peng-zhihui/L-ink_Card/DAP-Link/Firmware/src/source/cmsis-core/core_armv81mml.h

/**************************************************************************//**
 * @file     core_armv81mml.h
 * @brief    CMSIS Armv8.1-M Mainline Core Peripheral Access Layer Header File
 * @version  V1.2.0
 * @date     21. October 2019
 ******************************************************************************/
/*
 * Copyright (c) 2018-2019 Arm Limited. All rights reserved.
 *
 * SPDX-License-Identifier: Apache-2.0
 *
 * Licensed under the Apache License, Version 2.0 (the License); you may
 * not use this file except in compliance with the License.
 * You may obtain a copy of the License at
 *
 * www.apache.org/licenses/LICENSE-2.0
 *
 * Unless required by applicable law or agreed to in writing, software
 * distributed under the License is distributed on an AS IS BASIS, WITHOUT
 * WARRANTIES OR CONDITIONS OF ANY KIND, either express or implied.
 * See the License for the specific language governing permissions and
 * limitations under the License.
 */

#if   defined ( __ICCARM__ )
  #pragma system_include         /* treat file as system include file for MISRA check */
#elif defined (__clang__)
  #pragma clang system_header   /* treat file as system include file */
#endif

#ifndef __CORE_ARMV81MML_H_GENERIC
#define __CORE_ARMV81MML_H_GENERIC

#include <stdint.h>

#ifdef __cplusplus
 extern "C" {
#endif

/**
  \page CMSIS_MISRA_Exceptions  MISRA-C:2004 Compliance Exceptions
  CMSIS violates the following MISRA-C:2004 rules:

   \li Required Rule 8.5, object/function definition in header file.<br>
     Function definitions in header files are used to allow 'inlining'.

   \li Required Rule 18.4, declaration of union type or object of union type: '{...}'.<br>
     Unions are used for effective representation of core registers.

   \li Advisory Rule 19.7, Function-like macro defined.<br>
     Function-like macros are used to allow more efficient code.
 */


/*******************************************************************************
 *                 CMSIS definitions
 ******************************************************************************/
/**
  \ingroup Cortex_ARMV81MML
  @{
 */

#include "cmsis_version.h"
 
#define __ARM_ARCH_8M_MAIN__    1  // patching for now
/*  CMSIS ARMV81MML definitions */
#define __ARMv81MML_CMSIS_VERSION_MAIN  (__CM_CMSIS_VERSION_MAIN)                   /*!< \deprecated [31:16] CMSIS HAL main version */
#define __ARMv81MML_CMSIS_VERSION_SUB   (__CM_CMSIS_VERSION_SUB)                    /*!< \deprecated [15:0]  CMSIS HAL sub version */
#define __ARMv81MML_CMSIS_VERSION       ((__ARMv81MML_CMSIS_VERSION_MAIN << 16U) | \
                                         __ARMv81MML_CMSIS_VERSION_SUB           )  /*!< \deprecated CMSIS HAL version number */

#define __CORTEX_M                     (81U)                                       /*!< Cortex-M Core */

#if defined ( __CC_ARM )
  #error Legacy Arm Compiler does not support Armv8.1-M target architecture.
#elif defined (__ARMCC_VERSION) && (__ARMCC_VERSION >= 6010050)
  #if defined __ARM_FP
    #if defined (__FPU_PRESENT) && (__FPU_PRESENT == 1U)
      #define __FPU_USED       1U
    #else
      #error "Compiler generates FPU instructions for a device without an FPU (check __FPU_PRESENT)"
      #define __FPU_USED       0U
    #endif
  #else
    #define __FPU_USED         0U
  #endif

  #if defined(__ARM_FEATURE_DSP)
    #if defined(__DSP_PRESENT) && (__DSP_PRESENT == 1U)
      #define __DSP_USED       1U
    #else
      #error "Compiler generates DSP (SIMD) instructions for a devices without DSP extensions (check __DSP_PRESENT)"
      #define __DSP_USED         0U    
    #endif
  #else
    #define __DSP_USED         0U
  #endif
  
  #if defined(__ARM_FEATURE_MVE)
    #if defined(__MVE_PRESENT) && (__MVE_PRESENT == 1U)
      #define __MVE_USED       1U
    #else
      #error "Compiler generates MVE instructions for a devices without MVE extensions (check __MVE_PRESENT)"
      #define __MVE_USED         0U    
    #endif
  #else
    #define __MVE_USED         0U
  #endif

#elif defined ( __GNUC__ )
  #if defined (__VFP_FP__) && !defined(__SOFTFP__)
    #if defined (__FPU_PRESENT) && (__FPU_PRESENT == 1U)
      #define __FPU_USED       1U
    #else
      #error "Compiler generates FPU instructions for a device without an FPU (check __FPU_PRESENT)"
      #define __FPU_USED       0U
    #endif
  #else
    #define __FPU_USED         0U
  #endif
  
  #if defined(__ARM_FEATURE_DSP)
    #if defined(__DSP_PRESENT) && (__DSP_PRESENT == 1U)
      #define __DSP_USED       1U
    #else
      #error "Compiler generates DSP (SIMD) instructions for a devices without DSP extensions (check __DSP_PRESENT)"
      #define __DSP_USED         0U    
    #endif
  #else
    #define __DSP_USED         0U
  #endif
    
  #if defined(__ARM_FEATURE_MVE)
    #if defined(__MVE_PRESENT) && (__MVE_PRESENT == 1U)
      #define __MVE_USED       1U
    #else
      #error "Compiler generates MVE instructions for a devices without MVE extensions (check __MVE_PRESENT)"
      #define __MVE_USED         0U    
    #endif
  #else
    #define __MVE_USED         0U
  #endif
  
#elif defined ( __ICCARM__ )
  #if defined __ARMVFP__
    #if defined (__FPU_PRESENT) && (__FPU_PRESENT == 1U)
      #define __FPU_USED       1U
    #else
      #error "Compiler generates FPU instructions for a device without an FPU (check __FPU_PRESENT)"
      #define __FPU_USED       0U
    #endif
  #else
    #define __FPU_USED         0U
  #endif

  #if defined(__ARM_FEATURE_DSP)
    #if defined(__DSP_PRESENT) && (__DSP_PRESENT == 1U)
      #define __DSP_USED       1U
    #else
      #error "Compiler generates DSP (SIMD) instructions for a devices without DSP extensions (check __DSP_PRESENT)"
      #define __DSP_USED         0U    
    #endif
  #else
    #define __DSP_USED         0U
  #endif

  #if defined(__ARM_FEATURE_MVE)
    #if defined(__MVE_PRESENT) && (__MVE_PRESENT == 1U)
      #define __MVE_USED       1U
    #else
      #error "Compiler generates MVE instructions for a devices without MVE extensions (check __MVE_PRESENT)"
      #define __MVE_USED         0U    
    #endif
  #else
    #define __MVE_USED         0U
  #endif
  
#elif defined ( __TI_ARM__ )
  #if defined __TI_VFP_SUPPORT__
    #if defined (__FPU_PRESENT) && (__FPU_PRESENT == 1U)
      #define __FPU_USED       1U
    #else
      #error "Compiler generates FPU instructions for a device without an FPU (check __FPU_PRESENT)"
      #define __FPU_USED       0U
    #endif
  #else
    #define __FPU_USED         0U
  #endif

#elif defined ( __TASKING__ )
  #if defined __FPU_VFP__
    #if defined (__FPU_PRESENT) && (__FPU_PRESENT == 1U)
      #define __FPU_USED       1U
    #else
      #error "Compiler generates FPU instructions for a device without an FPU (check __FPU_PRESENT)"
      #define __FPU_USED       0U
    #endif
  #else
    #define __FPU_USED         0U
  #endif

#elif defined ( __CSMC__ )
  #if ( __CSMC__ & 0x400U)
    #if defined (__FPU_PRESENT) && (__FPU_PRESENT == 1U)
      #define __FPU_USED       1U
    #else
      #error "Compiler generates FPU instructions for a device without an FPU (check __FPU_PRESENT)"
      #define __FPU_USED       0U
    #endif
  #else
    #define __FPU_USED         0U
  #endif

#endif

#include "cmsis_compiler.h"               /* CMSIS compiler specific defines */


#ifdef __cplusplus
}
#endif

#endif /* __CORE_ARMV81MML_H_GENERIC */

#ifndef __CMSIS_GENERIC

#ifndef __CORE_ARMV81MML_H_DEPENDANT
#define __CORE_ARMV81MML_H_DEPENDANT

#ifdef __cplusplus
 extern "C" {
#endif

/* check device defines and use defaults */
#if defined __CHECK_DEVICE_DEFINES
  #ifndef __ARMv81MML_REV
    #define __ARMv81MML_REV               0x0000U
    #warning "__ARMv81MML_REV not defined in device header file; using default!"
  #endif

  #ifndef __FPU_PRESENT
    #define __FPU_PRESENT             0U
    #warning "__FPU_PRESENT not defined in device header file; using default!"
  #endif

  #ifndef __MPU_PRESENT
    #define __MPU_PRESENT             0U
    #warning "__MPU_PRESENT not defined in device header file; using default!"
  #endif

  #ifndef __SAUREGION_PRESENT
    #define __SAUREGION_PRESENT       0U
    #warning "__SAUREGION_PRESENT not defined in device header file; using default!"
  #endif

  #ifndef __DSP_PRESENT
    #define __DSP_PRESENT             0U
    #warning "__DSP_PRESENT not defined in device header file; using default!"
  #endif

  #ifndef __MVE_PRESENT
    #define __MVE_PRESENT             0U
    #warning "__MVE_PRESENT not defined in device header file; using default!"
  #endif

  #ifndef __NVIC_PRIO_BITS
    #define __NVIC_PRIO_BITS          3U
    #warning "__NVIC_PRIO_BITS not defined in device header file; using default!"
  #endif

  #ifndef __Vendor_SysTickConfig
    #define __Vendor_SysTickConfig    0U
    #warning "__Vendor_SysTickConfig not defined in device header file; using default!"
  #endif
#endif

/* IO definitions (access restrictions to peripheral registers) */
/**
    \defgroup CMSIS_glob_defs CMSIS Global Defines

    <strong>IO Type Qualifiers</strong> are used
    \li to specify the access to peripheral variables.
    \li for automatic generation of peripheral register debug information.
*/
#ifdef __cplusplus
  #define   __I     volatile             /*!< Defines 'read only' permissions */
#else
  #define   __I     volatile const       /*!< Defines 'read only' permissions */
#endif
#define     __O     volatile             /*!< Defines 'write only' permissions */
#define     __IO    volatile             /*!< Defines 'read / write' permissions */

/* following defines should be used for structure members */
#define     __IM     volatile const      /*! Defines 'read only' structure member permissions */
#define     __OM     volatile            /*! Defines 'write only' structure member permissions */
#define     __IOM    volatile            /*! Defines 'read / write' structure member permissions */

/*@} end of group ARMv81MML */



/*******************************************************************************
 *                 Register Abstraction
  Core Register contain:
  - Core Register
  - Core NVIC Register
  - Core SCB Register
  - Core SysTick Register
  - Core Debug Register
  - Core MPU Register
  - Core SAU Register
  - Core FPU Register
 ******************************************************************************/
/**
  \defgroup CMSIS_core_register Defines and Type Definitions
  \brief Type definitions and defines for Cortex-M processor based devices.
*/

/**
  \ingroup    CMSIS_core_register
  \defgroup   CMSIS_CORE  Status and Control Registers
  \brief      Core Register type definitions.
  @{
 */

/**
  \brief  Union type to access the Application Program Status Register (APSR).
 */
typedef union
{
  struct
  {
    uint32_t _reserved0:16;              /*!< bit:  0..15  Reserved */
    uint32_t GE:4;                       /*!< bit: 16..19  Greater than or Equal flags */
    uint32_t _reserved1:7;               /*!< bit: 20..26  Reserved */
    uint32_t Q:1;                        /*!< bit:     27  Saturation condition flag */
    uint32_t V:1;                        /*!< bit:     28  Overflow condition code flag */
    uint32_t C:1;                        /*!< bit:     29  Carry condition code flag */
    uint32_t Z:1;                        /*!< bit:     30  Zero condition code flag */
    uint32_t N:1;                        /*!< bit:     31  Negative condition code flag */
  } b;                                   /*!< Structure used for bit  access */
  uint32_t w;                            /*!< Type      used for word access */
} APSR_Type;

/* APSR Register Definitions */
#define APSR_N_Pos                         31U                                            /*!< APSR: N Position */
#define APSR_N_Msk                         (1UL << APSR_N_Pos)                            /*!< APSR: N Mask */

#define APSR_Z_Pos                         30U                                            /*!< APSR: Z Position */
#define APSR_Z_Msk                         (1UL << APSR_Z_Pos)                            /*!< APSR: Z Mask */

#define APSR_C_Pos                         29U                                            /*!< APSR: C Position */
#define APSR_C_Msk                         (1UL << APSR_C_Pos)                            /*!< APSR: C Mask */

#define APSR_V_Pos                         28U                                            /*!< APSR: V Position */
#define APSR_V_Msk                         (1UL << APSR_V_Pos)                            /*!< APSR: V Mask */

#define APSR_Q_Pos                         27U                                            /*!< APSR: Q Position */
#define APSR_Q_Msk                         (1UL << APSR_Q_Pos)                            /*!< APSR: Q Mask */

#define APSR_GE_Pos                        16U                                            /*!< APSR: GE Position */
#define APSR_GE_Msk                        (0xFUL << APSR_GE_Pos)                         /*!< APSR: GE Mask */


/**
  \brief  Union type to access the Interrupt Program Status Register (IPSR).
 */
typedef union
{
  struct
  {
    uint32_t ISR:9;                      /*!< bit:  0.. 8  Exception number */
    uint32_t _reserved0:23;              /*!< bit:  9..31  Reserved */
  } b;                                   /*!< Structure used for bit  access */
  uint32_t w;                            /*!< Type      used for word access */
} IPSR_Type;

/* IPSR Register Definitions */
#define IPSR_ISR_Pos                        0U                                            /*!< IPSR: ISR Position */
#define IPSR_ISR_Msk                       (0x1FFUL /*<< IPSR_ISR_Pos*/)                  /*!< IPSR: ISR Mask */


/**
  \brief  Union type to access the Special-Purpose Program Status Registers (xPSR).
 */
typedef union
{
  struct
  {
    uint32_t ISR:9;                      /*!< bit:  0.. 8  Exception number */
    uint32_t _reserved0:7;               /*!< bit:  9..15  Reserved */
    uint32_t GE:4;                       /*!< bit: 16..19  Greater than or Equal flags */
    uint32_t _reserved1:4;               /*!< bit: 20..23  Reserved */
    uint32_t T:1;                        /*!< bit:     24  Thumb bit        (read 0) */
    uint32_t IT:2;                       /*!< bit: 25..26  saved IT state   (read 0) */
    uint32_t Q:1;                        /*!< bit:     27  Saturation condition flag */
    uint32_t V:1;                        /*!< bit:     28  Overflow condition code flag */
    uint32_t C:1;                        /*!< bit:     29  Carry condition code flag */
    uint32_t Z:1;                        /*!< bit:     30  Zero condition code flag */
    uint32_t N:1;                        /*!< bit:     31  Negative condition code flag */
  } b;                                   /*!< Structure used for bit  access */
  uint32_t w;                            /*!< Type      used for word access */
} xPSR_Type;

/* xPSR Register Definitions */
#define xPSR_N_Pos                         31U                                            /*!< xPSR: N Position */
#define xPSR_N_Msk                         (1UL << xPSR_N_Pos)                            /*!< xPSR: N Mask */

#define xPSR_Z_Pos                         30U                                            /*!< xPSR: Z Position */
#define xPSR_Z_Msk                         (1UL << xPSR_Z_Pos)                            /*!< xPSR: Z Mask */

#define xPSR_C_Pos                         29U                                            /*!< xPSR: C Position */
#define xPSR_C_Msk                         (1UL << xPSR_C_Pos)                            /*!< xPSR: C Mask */

#define xPSR_V_Pos                         28U                                            /*!< xPSR: V Position */
#define xPSR_V_Msk                         (1UL << xPSR_V_Pos)                            /*!< xPSR: V Mask */

#define xPSR_Q_Pos                         27U                                            /*!< xPSR: Q Position */
#define xPSR_Q_Msk                         (1UL << xPSR_Q_Pos)                            /*!< xPSR: Q Mask */

#define xPSR_IT_Pos                        25U                                            /*!< xPSR: IT Position */
#define xPSR_IT_Msk                        (3UL << xPSR_IT_Pos)                           /*!< xPSR: IT Mask */

#define xPSR_T_Pos                         24U                                            /*!< xPSR: T Position */
#define xPSR_T_Msk                         (1UL << xPSR_T_Pos)                            /*!< xPSR: T Mask */

#define xPSR_GE_Pos                        16U                                            /*!< xPSR: GE Position */
#define xPSR_GE_Msk                        (0xFUL << xPSR_GE_Pos)                         /*!< xPSR: GE Mask */

#define xPSR_ISR_Pos                        0U                                            /*!< xPSR: ISR Position */
#define xPSR_ISR_Msk                       (0x1FFUL /*<< xPSR_ISR_Pos*/)                  /*!< xPSR: ISR Mask */


/**
  \brief  Union type to access the Control Registers (CONTROL).
 */
typedef union
{
  struct
  {
    uint32_t nPRIV:1;                    /*!< bit:      0  Execution privilege in Thread mode */
    uint32_t SPSEL:1;                    /*!< bit:      1  Stack-pointer select */
    uint32_t FPCA:1;                     /*!< bit:      2  Floating-point context active */
    uint32_t SFPA:1;                     /*!< bit:      3  Secure floating-point active */
    uint32_t _reserved1:28;              /*!< bit:  4..31  Reserved */
  } b;                                   /*!< Structure used for bit  access */
  uint32_t w;                            /*!< Type      used for word access */
} CONTROL_Type;

/* CONTROL Register Definitions */
#define CONTROL_SFPA_Pos                    3U                                            /*!< CONTROL: SFPA Position */
#define CONTROL_SFPA_Msk                   (1UL << CONTROL_SFPA_Pos)                      /*!< CONTROL: SFPA Mask */

#define CONTROL_FPCA_Pos                    2U                                            /*!< CONTROL: FPCA Position */
#define CONTROL_FPCA_Msk                   (1UL << CONTROL_FPCA_Pos)                      /*!< CONTROL: FPCA Mask */

#define CONTROL_SPSEL_Pos                   1U                                            /*!< CONTROL: SPSEL Position */
#define CONTROL_SPSEL_Msk                  (1UL << CONTROL_SPSEL_Pos)                     /*!< CONTROL: SPSEL Mask */

#define CONTROL_nPRIV_Pos                   0U                                            /*!< CONTROL: nPRIV Position */
#define CONTROL_nPRIV_Msk                  (1UL /*<< CONTROL_nPRIV_Pos*/)                 /*!< CONTROL: nPRIV Mask */

/*@} end of group CMSIS_CORE */


/**
  \ingroup    CMSIS_core_register
  \defgroup   CMSIS_NVIC  Nested Vectored Interrupt Controller (NVIC)
  \brief      Type definitions for the NVIC Registers
  @{
 */

/**
  \brief  Structure type to access the Nested Vectored Interrupt Controller (NVIC).
 */
typedef struct
{
  __IOM uint32_t ISER[16U];              /*!< Offset: 0x000 (R/W)  Interrupt Set Enable Register */
        uint32_t RESERVED0[16U];
  __IOM uint32_t ICER[16U];              /*!< Offset: 0x080 (R/W)  Interrupt Clear Enable Register */
        uint32_t RSERVED1[16U];
  __IOM uint32_t ISPR[16U];              /*!< Offset: 0x100 (R/W)  Interrupt Set Pending Register */
        uint32_t RESERVED2[16U];
  __IOM uint32_t ICPR[16U];              /*!< Offset: 0x180 (R/W)  Interrupt Clear Pending Register */
        uint32_t RESERVED3[16U];
  __IOM uint32_t IABR[16U];              /*!< Offset: 0x200 (R/W)  Interrupt Active bit Register */
        uint32_t RESERVED4[16U];
  __IOM uint32_t ITNS[16U];              /*!< Offset: 0x280 (R/W)  Interrupt Non-Secure State Register */
        uint32_t RESERVED5[16U];
  __IOM uint8_t  IPR[496U];              /*!< Offset: 0x300 (R/W)  Interrupt Priority Register (8Bit wide) */
        uint32_t RESERVED6[580U];
  __OM  uint32_t STIR;                   /*!< Offset: 0xE00 ( /W)  Software Trigger Interrupt Register */
}  NVIC_Type;

/* Software Triggered Interrupt Register Definitions */
#define NVIC_STIR_INTID_Pos                 0U                                         /*!< STIR: INTLINESNUM Position */
#define NVIC_STIR_INTID_Msk                (0x1FFUL /*<< NVIC_STIR_INTID_Pos*/)        /*!< STIR: INTLINESNUM Mask */

/*@} end of group CMSIS_NVIC */


/**
  \ingroup  CMSIS_core_register
  \defgroup CMSIS_SCB     System Control Block (SCB)
  \brief    Type definitions for the System Control Block Registers
  @{
 */

/**
  \brief  Structure type to access the System Control Block (SCB).
 */
typedef struct
{
  __IM  uint32_t CPUID;                  /*!< Offset: 0x000 (R/ )  CPUID Base Register */
  __IOM uint32_t ICSR;                   /*!< Offset: 0x004 (R/W)  Interrupt Control and State Register */
  __IOM uint32_t VTOR;                   /*!< Offset: 0x008 (R/W)  Vector Table Offset Register */
  __IOM uint32_t AIRCR;                  /*!< Offset: 0x00C (R/W)  Application Interrupt and Reset Control Register */
  __IOM uint32_t SCR;                    /*!< Offset: 0x010 (R/W)  System Control Register */
  __IOM uint32_t CCR;                    /*!< Offset: 0x014 (R/W)  Configuration Control Register */
  __IOM uint8_t  SHPR[12U];              /*!< Offset: 0x018 (R/W)  System Handlers Priority Registers (4-7, 8-11, 12-15) */
  __IOM uint32_t SHCSR;                  /*!< Offset: 0x024 (R/W)  System Handler Control and State Register */
  __IOM uint32_t CFSR;                   /*!< Offset: 0x028 (R/W)  Configurable Fault Status Register */
  __IOM uint32_t HFSR;                   /*!< Offset: 0x02C (R/W)  HardFault Status Register */
  __IOM uint32_t DFSR;                   /*!< Offset: 0x030 (R/W)  Debug Fault Status Register */
  __IOM uint32_t MMFAR;                  /*!< Offset: 0x034 (R/W)  MemManage Fault Address Register */
  __IOM uint32_t BFAR;                   /*!< Offset: 0x038 (R/W)  BusFault Address Register */
  __IOM uint32_t AFSR;                   /*!< Offset: 0x03C (R/W)  Auxiliary Fault Status Register */
  __IM  uint32_t ID_PFR[2U];             /*!< Offset: 0x040 (R/ )  Processor Feature Register */
  __IM  uint32_t ID_DFR;                 /*!< Offset: 0x048 (R/ )  Debug Feature Register */
  __IM  uint32_t ID_ADR;                 /*!< Offset: 0x04C (R/ )  Auxiliary Feature Register */
  __IM  uint32_t ID_MMFR[4U];            /*!< Offset: 0x050 (R/ )  Memory Model Feature Register */
  __IM  uint32_t ID_ISAR[6U];            /*!< Offset: 0x060 (R/ )  Instruction Set Attributes Register */
  __IM  uint32_t CLIDR;                  /*!< Offset: 0x078 (R/ )  Cache Level ID register */
  __IM  uint32_t CTR;                    /*!< Offset: 0x07C (R/ )  Cache Type register */
  __IM  uint32_t CCSIDR;                 /*!< Offset: 0x080 (R/ )  Cache Size ID Register */
  __IOM uint32_t CSSELR;                 /*!< Offset: 0x084 (R/W)  Cache Size Selection Register */
  __IOM uint32_t CPACR;                  /*!< Offset: 0x088 (R/W)  Coprocessor Access Control Register */
  __IOM uint32_t NSACR;                  /*!< Offset: 0x08C (R/W)  Non-Secure Access Control Register */
        uint32_t RESERVED3[92U];
  __OM  uint32_t STIR;                   /*!< Offset: 0x200 ( /W)  Software Triggered Interrupt Register */
  __IOM uint32_t RFSR;                   /*!< Offset: 0x204 (R/W)  RAS Fault Status Register */
        uint32_t RESERVED4[14U];
  __IM  uint32_t MVFR0;                  /*!< Offset: 0x240 (R/ )  Media and VFP Feature Register 0 */
  __IM  uint32_t MVFR1;                  /*!< Offset: 0x244 (R/ )  Media and VFP Feature Register 1 */
  __IM  uint32_t MVFR2;                  /*!< Offset: 0x248 (R/ )  Media and VFP Feature Register 2 */
        uint32_t RESERVED5[1U];
  __OM  uint32_t ICIALLU;                /*!< Offset: 0x250 ( /W)  I-Cache Invalidate All to PoU */
        uint32_t RESERVED6[1U];
  __OM  uint32_t ICIMVAU;                /*!< Offset: 0x258 ( /W)  I-Cache Invalidate by MVA to PoU */
  __OM  uint32_t DCIMVAC;                /*!< Offset: 0x25C ( /W)  D-Cache Invalidate by MVA to PoC */
  __OM  uint32_t DCISW;                  /*!< Offset: 0x260 ( /W)  D-Cache Invalidate by Set-way */
  __OM  uint32_t DCCMVAU;                /*!< Offset: 0x264 ( /W)  D-Cache Clean by MVA to PoU */
  __OM  uint32_t DCCMVAC;                /*!< Offset: 0x268 ( /W)  D-Cache Clean by MVA to PoC */
  __OM  uint32_t DCCSW;                  /*!< Offset: 0x26C ( /W)  D-Cache Clean by Set-way */
  __OM  uint32_t DCCIMVAC;               /*!< Offset: 0x270 ( /W)  D-Cache Clean and Invalidate by MVA to PoC */
  __OM  uint32_t DCCISW;                 /*!< Offset: 0x274 ( /W)  D-Cache Clean and Invalidate by Set-way */
  __OM  uint32_t BPIALL;                 /*!< Offset: 0x278 ( /W)  Branch Predictor Invalidate All */
} SCB_Type;

/* SCB CPUID Register Definitions */
#define SCB_CPUID_IMPLEMENTER_Pos          24U                                            /*!< SCB CPUID: IMPLEMENTER Position */
#define SCB_CPUID_IMPLEMENTER_Msk          (0xFFUL << SCB_CPUID_IMPLEMENTER_Pos)          /*!< SCB CPUID: IMPLEMENTER Mask */

#define SCB_CPUID_VARIANT_Pos              20U                                            /*!< SCB CPUID: VARIANT Position */
#define SCB_CPUID_VARIANT_Msk              (0xFUL << SCB_CPUID_VARIANT_Pos)               /*!< SCB CPUID: VARIANT Mask */

#define SCB_CPUID_ARCHITECTURE_Pos         16U                                            /*!< SCB CPUID: ARCHITECTURE Position */
#define SCB_CPUID_ARCHITECTURE_Msk         (0xFUL << SCB_CPUID_ARCHITECTURE_Pos)          /*!< SCB CPUID: ARCHITECTURE Mask */

#define SCB_CPUID_PARTNO_Pos                4U                                            /*!< SCB CPUID: PARTNO Position */
#define SCB_CPUID_PARTNO_Msk               (0xFFFUL << SCB_CPUID_PARTNO_Pos)              /*!< SCB CPUID: PARTNO Mask */

#define SCB_CPUID_REVISION_Pos              0U                                            /*!< SCB CPUID: REVISION Position */
#define SCB_CPUID_REVISION_Msk             (0xFUL /*<< SCB_CPUID_REVISION_Pos*/)          /*!< SCB CPUID: REVISION Mask */

/* SCB Interrupt Control State Register Definitions */
#define SCB_ICSR_PENDNMISET_Pos            31U                                            /*!< SCB ICSR: PENDNMISET Position */
#define SCB_ICSR_PENDNMISET_Msk            (1UL << SCB_ICSR_PENDNMISET_Pos)               /*!< SCB ICSR: PENDNMISET Mask */

#define SCB_ICSR_NMIPENDSET_Pos            SCB_ICSR_PENDNMISET_Pos                        /*!< SCB ICSR: NMIPENDSET Position, backward compatibility */
#define SCB_ICSR_NMIPENDSET_Msk            SCB_ICSR_PENDNMISET_Msk                        /*!< SCB ICSR: NMIPENDSET Mask, backward compatibility */

#define SCB_ICSR_PENDNMICLR_Pos            30U                                            /*!< SCB ICSR: PENDNMICLR Position */
#define SCB_ICSR_PENDNMICLR_Msk            (1UL << SCB_ICSR_PENDNMICLR_Pos)               /*!< SCB ICSR: PENDNMICLR Mask */

#define SCB_ICSR_PENDSVSET_Pos             28U                                            /*!< SCB ICSR: PENDSVSET Position */
#define SCB_ICSR_PENDSVSET_Msk             (1UL << SCB_ICSR_PENDSVSET_Pos)                /*!< SCB ICSR: PENDSVSET Mask */

#define SCB_ICSR_PENDSVCLR_Pos             27U                                            /*!< SCB ICSR: PENDSVCLR Position */
#define SCB_ICSR_PENDSVCLR_Msk             (1UL << SCB_ICSR_PENDSVCLR_Pos)                /*!< SCB ICSR: PENDSVCLR Mask */

#define SCB_ICSR_PENDSTSET_Pos             26U                                            /*!< SCB ICSR: PENDSTSET Position */
#define SCB_ICSR_PENDSTSET_Msk             (1UL << SCB_ICSR_PENDSTSET_Pos)                /*!< SCB ICSR: PENDSTSET Mask */

#define SCB_ICSR_PENDSTCLR_Pos             25U                                            /*!< SCB ICSR: PENDSTCLR Position */
#define SCB_ICSR_PENDSTCLR_Msk             (1UL << SCB_ICSR_PENDSTCLR_Pos)                /*!< SCB ICSR: PENDSTCLR Mask */

#define SCB_ICSR_STTNS_Pos                 24U                                            /*!< SCB ICSR: STTNS Position (Security Extension) */
#define SCB_ICSR_STTNS_Msk                 (1UL << SCB_ICSR_STTNS_Pos)                    /*!< SCB ICSR: STTNS Mask (Security Extension) */

#define SCB_ICSR_ISRPREEMPT_Pos            23U                                            /*!< SCB ICSR: ISRPREEMPT Position */
#define SCB_ICSR_ISRPREEMPT_Msk            (1UL << SCB_ICSR_ISRPREEMPT_Pos)               /*!< SCB ICSR: ISRPREEMPT Mask */

#define SCB_ICSR_ISRPENDING_Pos            22U                                            /*!< SCB ICSR: ISRPENDING Position */
#define SCB_ICSR_ISRPENDING_Msk            (1UL << SCB_ICSR_ISRPENDING_Pos)               /*!< SCB ICSR: ISRPENDING Mask */

#define SCB_ICSR_VECTPENDING_Pos           12U                                            /*!< SCB ICSR: VECTPENDING Position */
#define SCB_ICSR_VECTPENDING_Msk           (0x1FFUL << SCB_ICSR_VECTPENDING_Pos)          /*!< SCB ICSR: VECTPENDING Mask */

#define SCB_ICSR_RETTOBASE_Pos             11U                                            /*!< SCB ICSR: RETTOBASE Position */
#define SCB_ICSR_RETTOBASE_Msk             (1UL << SCB_ICSR_RETTOBASE_Pos)                /*!< SCB ICSR: RETTOBASE Mask */

#define SCB_ICSR_VECTACTIVE_Pos             0U                                            /*!< SCB ICSR: VECTACTIVE Position */
#define SCB_ICSR_VECTACTIVE_Msk            (0x1FFUL /*<< SCB_ICSR_VECTACTIVE_Pos*/)       /*!< SCB ICSR: VECTACTIVE Mask */

/* SCB Vector Table Offset Register Definitions */
#define SCB_VTOR_TBLOFF_Pos                 7U                                            /*!< SCB VTOR: TBLOFF Position */
#define SCB_VTOR_TBLOFF_Msk                (0x1FFFFFFUL << SCB_VTOR_TBLOFF_Pos)           /*!< SCB VTOR: TBLOFF Mask */

/* SCB Application Interrupt and Reset Control Register Definitions */
#define SCB_AIRCR_VECTKEY_Pos              16U                                            /*!< SCB AIRCR: VECTKEY Position */
#define SCB_AIRCR_VECTKEY_Msk              (0xFFFFUL << SCB_AIRCR_VECTKEY_Pos)            /*!< SCB AIRCR: VECTKEY Mask */

#define SCB_AIRCR_VECTKEYSTAT_Pos          16U                                            /*!< SCB AIRCR: VECTKEYSTAT Position */
#define SCB_AIRCR_VECTKEYSTAT_Msk          (0xFFFFUL << SCB_AIRCR_VECTKEYSTAT_Pos)        /*!< SCB AIRCR: VECTKEYSTAT Mask */

#define SCB_AIRCR_ENDIANESS_Pos            15U                                            /*!< SCB AIRCR: ENDIANESS Position */
#define SCB_AIRCR_ENDIANESS_Msk            (1UL << SCB_AIRCR_ENDIANESS_Pos)               /*!< SCB AIRCR: ENDIANESS Mask */

#define SCB_AIRCR_PRIS_Pos                 14U                                            /*!< SCB AIRCR: PRIS Position */
#define SCB_AIRCR_PRIS_Msk                 (1UL << SCB_AIRCR_PRIS_Pos)                    /*!< SCB AIRCR: PRIS Mask */

#define SCB_AIRCR_BFHFNMINS_Pos            13U                                            /*!< SCB AIRCR: BFHFNMINS Position */
#define SCB_AIRCR_BFHFNMINS_Msk            (1UL << SCB_AIRCR_BFHFNMINS_Pos)               /*!< SCB AIRCR: BFHFNMINS Mask */

#define SCB_AIRCR_PRIGROUP_Pos              8U                                            /*!< SCB AIRCR: PRIGROUP Position */
#define SCB_AIRCR_PRIGROUP_Msk             (7UL << SCB_AIRCR_PRIGROUP_Pos)                /*!< SCB AIRCR: PRIGROUP Mask */

#define SCB_AIRCR_IESB_Pos                  5U                                            /*!< SCB AIRCR: Implicit ESB Enable Position */
#define SCB_AIRCR_IESB_Msk                 (1UL << SCB_AIRCR_IESB_Pos)                    /*!< SCB AIRCR: Implicit ESB Enable Mask */

#define SCB_AIRCR_DIT_Pos                   4U                                            /*!< SCB AIRCR: Data Independent Timing Position */
#define SCB_AIRCR_DIT_Msk                  (1UL << SCB_AIRCR_DIT_Pos)                     /*!< SCB AIRCR: Data Independent Timing Mask */

#define SCB_AIRCR_SYSRESETREQS_Pos          3U                                            /*!< SCB AIRCR: SYSRESETREQS Position */
#define SCB_AIRCR_SYSRESETREQS_Msk         (1UL << SCB_AIRCR_SYSRESETREQS_Pos)            /*!< SCB AIRCR: SYSRESETREQS Mask */

#define SCB_AIRCR_SYSRESETREQ_Pos           2U                                            /*!< SCB AIRCR: SYSRESETREQ Position */
#define SCB_AIRCR_SYSRESETREQ_Msk          (1UL << SCB_AIRCR_SYSRESETREQ_Pos)             /*!< SCB AIRCR: SYSRESETREQ Mask */

#define SCB_AIRCR_VECTCLRACTIVE_Pos         1U                                            /*!< SCB AIRCR: VECTCLRACTIVE Position */
#define SCB_AIRCR_VECTCLRACTIVE_Msk        (1UL << SCB_AIRCR_VECTCLRACTIVE_Pos)           /*!< SCB AIRCR: VECTCLRACTIVE Mask */

/* SCB System Control Register Definitions */
#define SCB_SCR_SEVONPEND_Pos               4U                                            /*!< SCB SCR: SEVONPEND Position */
#define SCB_SCR_SEVONPEND_Msk              (1UL << SCB_SCR_SEVONPEND_Pos)                 /*!< SCB SCR: SEVONPEND Mask */

#define SCB_SCR_SLEEPDEEPS_Pos              3U                                            /*!< SCB SCR: SLEEPDEEPS Position */
#define SCB_SCR_SLEEPDEEPS_Msk             (1UL << SCB_SCR_SLEEPDEEPS_Pos)                /*!< SCB SCR: SLEEPDEEPS Mask */

#define SCB_SCR_SLEEPDEEP_Pos               2U                                            /*!< SCB SCR: SLEEPDEEP Position */
#define SCB_SCR_SLEEPDEEP_Msk              (1UL << SCB_SCR_SLEEPDEEP_Pos)                 /*!< SCB SCR: SLEEPDEEP Mask */

#define SCB_SCR_SLEEPONEXIT_Pos             1U                                            /*!< SCB SCR: SLEEPONEXIT Position */
#define SCB_SCR_SLEEPONEXIT_Msk            (1UL << SCB_SCR_SLEEPONEXIT_Pos)               /*!< SCB SCR: SLEEPONEXIT Mask */

/* SCB Configuration Control Register Definitions */
#define SCB_CCR_TRD_Pos                    20U                                            /*!< SCB CCR: TRD Position */
#define SCB_CCR_TRD_Msk                    (1UL << SCB_CCR_TRD_Pos)                       /*!< SCB CCR: TRD Mask */

#define SCB_CCR_LOB_Pos                    19U                                            /*!< SCB CCR: LOB Position */
#define SCB_CCR_LOB_Msk                    (1UL << SCB_CCR_LOB_Pos)                       /*!< SCB CCR: LOB Mask */

#define SCB_CCR_BP_Pos                     18U                                            /*!< SCB CCR: BP Position */
#define SCB_CCR_BP_Msk                     (1UL << SCB_CCR_BP_Pos)                        /*!< SCB CCR: BP Mask */

#define SCB_CCR_IC_Pos                     17U                                            /*!< SCB CCR: IC Position */
#define SCB_CCR_IC_Msk                     (1UL << SCB_CCR_IC_Pos)                        /*!< SCB CCR: IC Mask */

#define SCB_CCR_DC_Pos                     16U                                            /*!< SCB CCR: DC Position */
#define SCB_CCR_DC_Msk                     (1UL << SCB_CCR_DC_Pos)                        /*!< SCB CCR: DC Mask */

#define SCB_CCR_STKOFHFNMIGN_Pos           10U                                            /*!< SCB CCR: STKOFHFNMIGN Position */
#define SCB_CCR_STKOFHFNMIGN_Msk           (1UL << SCB_CCR_STKOFHFNMIGN_Pos)              /*!< SCB CCR: STKOFHFNMIGN Mask */

#define SCB_CCR_BFHFNMIGN_Pos               8U                                            /*!< SCB CCR: BFHFNMIGN Position */
#define SCB_CCR_BFHFNMIGN_Msk              (1UL << SCB_CCR_BFHFNMIGN_Pos)                 /*!< SCB CCR: BFHFNMIGN Mask */

#define SCB_CCR_DIV_0_TRP_Pos               4U                                            /*!< SCB CCR: DIV_0_TRP Position */
#define SCB_CCR_DIV_0_TRP_Msk              (1UL << SCB_CCR_DIV_0_TRP_Pos)                 /*!< SCB CCR: DIV_0_TRP Mask */

#define SCB_CCR_UNALIGN_TRP_Pos             3U                                            /*!< SCB CCR: UNALIGN_TRP Position */
#define SCB_CCR_UNALIGN_TRP_Msk            (1UL << SCB_CCR_UNALIGN_TRP_Pos)               /*!< SCB CCR: UNALIGN_TRP Mask */

#define SCB_CCR_USERSETMPEND_Pos            1U                                            /*!< SCB CCR: USERSETMPEND Position */
#define SCB_CCR_USERSETMPEND_Msk           (1UL << SCB_CCR_USERSETMPEND_Pos)              /*!< SCB CCR: USERSETMPEND Mask */

/* SCB System Handler Control and State Register Definitions */
#define SCB_SHCSR_HARDFAULTPENDED_Pos      21U                                            /*!< SCB SHCSR: HARDFAULTPENDED Position */
#define SCB_SHCSR_HARDFAULTPENDED_Msk      (1UL << SCB_SHCSR_HARDFAULTPENDED_Pos)         /*!< SCB SHCSR: HARDFAULTPENDED Mask */

#define SCB_SHCSR_SECUREFAULTPENDED_Pos    20U                                            /*!< SCB SHCSR: SECUREFAULTPENDED Position */
#define SCB_SHCSR_SECUREFAULTPENDED_Msk    (1UL << SCB_SHCSR_SECUREFAULTPENDED_Pos)       /*!< SCB SHCSR: SECUREFAULTPENDED Mask */

#define SCB_SHCSR_SECUREFAULTENA_Pos       19U                                            /*!< SCB SHCSR: SECUREFAULTENA Position */
#define SCB_SHCSR_SECUREFAULTENA_Msk       (1UL << SCB_SHCSR_SECUREFAULTENA_Pos)          /*!< SCB SHCSR: SECUREFAULTENA Mask */

#define SCB_SHCSR_USGFAULTENA_Pos          18U                                            /*!< SCB SHCSR: USGFAULTENA Position */
#define SCB_SHCSR_USGFAULTENA_Msk          (1UL << SCB_SHCSR_USGFAULTENA_Pos)             /*!< SCB SHCSR: USGFAULTENA Mask */

#define SCB_SHCSR_BUSFAULTENA_Pos          17U                                            /*!< SCB SHCSR: BUSFAULTENA Position */
#define SCB_SHCSR_BUSFAULTENA_Msk          (1UL << SCB_SHCSR_BUSFAULTENA_Pos)             /*!< SCB SHCSR: BUSFAULTENA Mask */

#define SCB_SHCSR_MEMFAULTENA_Pos          16U                                            /*!< SCB SHCSR: MEMFAULTENA Position */
#define SCB_SHCSR_MEMFAULTENA_Msk          (1UL << SCB_SHCSR_MEMFAULTENA_Pos)             /*!< SCB SHCSR: MEMFAULTENA Mask */

#define SCB_SHCSR_SVCALLPENDED_Pos         15U                                            /*!< SCB SHCSR: SVCALLPENDED Position */
#define SCB_SHCSR_SVCALLPENDED_Msk         (1UL << SCB_SHCSR_SVCALLPENDED_Pos)            /*!< SCB SHCSR: SVCALLPENDED Mask */

#define SCB_SHCSR_BUSFAULTPENDED_Pos       14U                                            /*!< SCB SHCSR: BUSFAULTPENDED Position */
#define SCB_SHCSR_BUSFAULTPENDED_Msk       (1UL << SCB_SHCSR_BUSFAULTPENDED_Pos)          /*!< SCB SHCSR: BUSFAULTPENDED Mask */

#define SCB_SHCSR_MEMFAULTPENDED_Pos       13U                                            /*!< SCB SHCSR: MEMFAULTPENDED Position */
#define SCB_SHCSR_MEMFAULTPENDED_Msk       (1UL << SCB_SHCSR_MEMFAULTPENDED_Pos)          /*!< SCB SHCSR: MEMFAULTPENDED Mask */

#define SCB_SHCSR_USGFAULTPENDED_Pos       12U                                            /*!< SCB SHCSR: USGFAULTPENDED Position */
#define SCB_SHCSR_USGFAULTPENDED_Msk       (1UL << SCB_SHCSR_USGFAULTPENDED_Pos)          /*!< SCB SHCSR: USGFAULTPENDED Mask */

#define SCB_SHCSR_SYSTICKACT_Pos           11U                                            /*!< SCB SHCSR: SYSTICKACT Position */
#define SCB_SHCSR_SYSTICKACT_Msk           (1UL << SCB_SHCSR_SYSTICKACT_Pos)              /*!< SCB SHCSR: SYSTICKACT Mask */

#define SCB_SHCSR_PENDSVACT_Pos            10U                                            /*!< SCB SHCSR: PENDSVACT Position */
#define SCB_SHCSR_PENDSVACT_Msk            (1UL << SCB_SHCSR_PENDSVACT_Pos)               /*!< SCB SHCSR: PENDSVACT Mask */

#define SCB_SHCSR_MONITORACT_Pos            8U                                            /*!< SCB SHCSR: MONITORACT Position */
#define SCB_SHCSR_MONITORACT_Msk           (1UL << SCB_SHCSR_MONITORACT_Pos)              /*!< SCB SHCSR: MONITORACT Mask */

#define SCB_SHCSR_SVCALLACT_Pos             7U                                            /*!< SCB SHCSR: SVCALLACT Position */
#define SCB_SHCSR_SVCALLACT_Msk            (1UL << SCB_SHCSR_SVCALLACT_Pos)               /*!< SCB SHCSR: SVCALLACT Mask */

#define SCB_SHCSR_NMIACT_Pos                5U                                            /*!< SCB SHCSR: NMIACT Position */
#define SCB_SHCSR_NMIACT_Msk               (1UL << SCB_SHCSR_NMIACT_Pos)                  /*!< SCB SHCSR: NMIACT Mask */

#define SCB_SHCSR_SECUREFAULTACT_Pos        4U                                            /*!< SCB SHCSR: SECUREFAULTACT Position */
#define SCB_SHCSR_SECUREFAULTACT_Msk       (1UL << SCB_SHCSR_SECUREFAULTACT_Pos)          /*!< SCB SHCSR: SECUREFAULTACT Mask */

#define SCB_SHCSR_USGFAULTACT_Pos           3U                                            /*!< SCB SHCSR: USGFAULTACT Position */
#define SCB_SHCSR_USGFAULTACT_Msk          (1UL << SCB_SHCSR_USGFAULTACT_Pos)             /*!< SCB SHCSR: USGFAULTACT Mask */

#define SCB_SHCSR_HARDFAULTACT_Pos          2U                                            /*!< SCB SHCSR: HARDFAULTACT Position */
#define SCB_SHCSR_HARDFAULTACT_Msk         (1UL << SCB_SHCSR_HARDFAULTACT_Pos)            /*!< SCB SHCSR: HARDFAULTACT Mask */

#define SCB_SHCSR_BUSFAULTACT_Pos           1U                                            /*!< SCB SHCSR: BUSFAULTACT Position */
#define SCB_SHCSR_BUSFAULTACT_Msk          (1UL << SCB_SHCSR_BUSFAULTACT_Pos)             /*!< SCB SHCSR: BUSFAULTACT Mask */

#define SCB_SHCSR_MEMFAULTACT_Pos           0U                                            /*!< SCB SHCSR: MEMFAULTACT Position */
#define SCB_SHCSR_MEMFAULTACT_Msk          (1UL /*<< SCB_SHCSR_MEMFAULTACT_Pos*/)         /*!< SCB SHCSR: MEMFAULTACT Mask */

/* SCB Configurable Fault Status Register Definitions */
#define SCB_CFSR_USGFAULTSR_Pos            16U                                            /*!< SCB CFSR: Usage Fault Status Register Position */
#define SCB_CFSR_USGFAULTSR_Msk            (0xFFFFUL << SCB_CFSR_USGFAULTSR_Pos)          /*!< SCB CFSR: Usage Fault Status Register Mask */

#define SCB_CFSR_BUSFAULTSR_Pos             8U                                            /*!< SCB CFSR: Bus Fault Status Register Position */
#define SCB_CFSR_BUSFAULTSR_Msk            (0xFFUL << SCB_CFSR_BUSFAULTSR_Pos)            /*!< SCB CFSR: Bus Fault Status Register Mask */

#define SCB_CFSR_MEMFAULTSR_Pos             0U                                            /*!< SCB CFSR: Memory Manage Fault Status Register Position */
#define SCB_CFSR_MEMFAULTSR_Msk            (0xFFUL /*<< SCB_CFSR_MEMFAULTSR_Pos*/)        /*!< SCB CFSR: Memory Manage Fault Status Register Mask */

/* MemManage Fault Status Register (part of SCB Configurable Fault Status Register) */
#define SCB_CFSR_MMARVALID_Pos             (SCB_SHCSR_MEMFAULTACT_Pos + 7U)               /*!< SCB CFSR (MMFSR): MMARVALID Position */
#define SCB_CFSR_MMARVALID_Msk             (1UL << SCB_CFSR_MMARVALID_Pos)                /*!< SCB CFSR (MMFSR): MMARVALID Mask */

#define SCB_CFSR_MLSPERR_Pos               (SCB_SHCSR_MEMFAULTACT_Pos + 5U)               /*!< SCB CFSR (MMFSR): MLSPERR Position */
#define SCB_CFSR_MLSPERR_Msk               (1UL << SCB_CFSR_MLSPERR_Pos)                  /*!< SCB CFSR (MMFSR): MLSPERR Mask */

#define SCB_CFSR_MSTKERR_Pos               (SCB_SHCSR_MEMFAULTACT_Pos + 4U)               /*!< SCB CFSR (MMFSR): MSTKERR Position */
#define SCB_CFSR_MSTKERR_Msk               (1UL << SCB_CFSR_MSTKERR_Pos)                  /*!< SCB CFSR (MMFSR): MSTKERR Mask */

#define SCB_CFSR_MUNSTKERR_Pos             (SCB_SHCSR_MEMFAULTACT_Pos + 3U)               /*!< SCB CFSR (MMFSR): MUNSTKERR Position */
#define SCB_CFSR_MUNSTKERR_Msk             (1UL << SCB_CFSR_MUNSTKERR_Pos)                /*!< SCB CFSR (MMFSR): MUNSTKERR Mask */

#define SCB_CFSR_DACCVIOL_Pos              (SCB_SHCSR_MEMFAULTACT_Pos + 1U)               /*!< SCB CFSR (MMFSR): DACCVIOL Position */
#define SCB_CFSR_DACCVIOL_Msk              (1UL << SCB_CFSR_DACCVIOL_Pos)                 /*!< SCB CFSR (MMFSR): DACCVIOL Mask */

#define SCB_CFSR_IACCVIOL_Pos              (SCB_SHCSR_MEMFAULTACT_Pos + 0U)               /*!< SCB CFSR (MMFSR): IACCVIOL Position */
#define SCB_CFSR_IACCVIOL_Msk              (1UL /*<< SCB_CFSR_IACCVIOL_Pos*/)             /*!< SCB CFSR (MMFSR): IACCVIOL Mask */

/* BusFault Status Register (part of SCB Configurable Fault Status Register) */
#define SCB_CFSR_BFARVALID_Pos            (SCB_CFSR_BUSFAULTSR_Pos + 7U)                  /*!< SCB CFSR (BFSR): BFARVALID Position */
#define SCB_CFSR_BFARVALID_Msk            (1UL << SCB_CFSR_BFARVALID_Pos)                 /*!< SCB CFSR (BFSR): BFARVALID Mask */

#define SCB_CFSR_LSPERR_Pos               (SCB_CFSR_BUSFAULTSR_Pos + 5U)                  /*!< SCB CFSR (BFSR): LSPERR Position */
#define SCB_CFSR_LSPERR_Msk               (1UL << SCB_CFSR_LSPERR_Pos)                    /*!< SCB CFSR (BFSR): LSPERR Mask */

#define SCB_CFSR_STKERR_Pos               (SCB_CFSR_BUSFAULTSR_Pos + 4U)                  /*!< SCB CFSR (BFSR): STKERR Position */
#define SCB_CFSR_STKERR_Msk               (1UL << SCB_CFSR_STKERR_Pos)                    /*!< SCB CFSR (BFSR): STKERR Mask */

#define SCB_CFSR_UNSTKERR_Pos             (SCB_CFSR_BUSFAULTSR_Pos + 3U)                  /*!< SCB CFSR (BFSR): UNSTKERR Position */
#define SCB_CFSR_UNSTKERR_Msk             (1UL << SCB_CFSR_UNSTKERR_Pos)                  /*!< SCB CFSR (BFSR): UNSTKERR Mask */

#define SCB_CFSR_IMPRECISERR_Pos          (SCB_CFSR_BUSFAULTSR_Pos + 2U)                  /*!< SCB CFSR (BFSR): IMPRECISERR Position */
#define SCB_CFSR_IMPRECISERR_Msk          (1UL << SCB_CFSR_IMPRECISERR_Pos)               /*!< SCB CFSR (BFSR): IMPRECISERR Mask */

#define SCB_CFSR_PRECISERR_Pos            (SCB_CFSR_BUSFAULTSR_Pos + 1U)                  /*!< SCB CFSR (BFSR): PRECISERR Position */
#define SCB_CFSR_PRECISERR_Msk            (1UL << SCB_CFSR_PRECISERR_Pos)                 /*!< SCB CFSR (BFSR): PRECISERR Mask */

#define SCB_CFSR_IBUSERR_Pos              (SCB_CFSR_BUSFAULTSR_Pos + 0U)                  /*!< SCB CFSR (BFSR): IBUSERR Position */
#define SCB_CFSR_IBUSERR_Msk              (1UL << SCB_CFSR_IBUSERR_Pos)                   /*!< SCB CFSR (BFSR): IBUSERR Mask */

/* UsageFault Status Register (part of SCB Configurable Fault Status Register) */
#define SCB_CFSR_DIVBYZERO_Pos            (SCB_CFSR_USGFAULTSR_Pos + 9U)                  /*!< SCB CFSR (UFSR): DIVBYZERO Position */
#define SCB_CFSR_DIVBYZERO_Msk            (1UL << SCB_CFSR_DIVBYZERO_Pos)                 /*!< SCB CFSR (UFSR): DIVBYZERO Mask */

#define SCB_CFSR_UNALIGNED_Pos            (SCB_CFSR_USGFAULTSR_Pos + 8U)                  /*!< SCB CFSR (UFSR): UNALIGNED Position */
#define SCB_CFSR_UNALIGNED_Msk            (1UL << SCB_CFSR_UNALIGNED_Pos)                 /*!< SCB CFSR (UFSR): UNALIGNED Mask */

#define SCB_CFSR_STKOF_Pos                (SCB_CFSR_USGFAULTSR_Pos + 4U)                  /*!< SCB CFSR (UFSR): STKOF Position */
#define SCB_CFSR_STKOF_Msk                (1UL << SCB_CFSR_STKOF_Pos)                     /*!< SCB CFSR (UFSR): STKOF Mask */

#define SCB_CFSR_NOCP_Pos                 (SCB_CFSR_USGFAULTSR_Pos + 3U)                  /*!< SCB CFSR (UFSR): NOCP Position */
#define SCB_CFSR_NOCP_Msk                 (1UL << SCB_CFSR_NOCP_Pos)                      /*!< SCB CFSR (UFSR): NOCP Mask */

#define SCB_CFSR_INVPC_Pos                (SCB_CFSR_USGFAULTSR_Pos + 2U)                  /*!< SCB CFSR (UFSR): INVPC Position */
#define SCB_CFSR_INVPC_Msk                (1UL << SCB_CFSR_INVPC_Pos)                     /*!< SCB CFSR (UFSR): INVPC Mask */

#define SCB_CFSR_INVSTATE_Pos             (SCB_CFSR_USGFAULTSR_Pos + 1U)                  /*!< SCB CFSR (UFSR): INVSTATE Position */
#define SCB_CFSR_INVSTATE_Msk             (1UL << SCB_CFSR_INVSTATE_Pos)                  /*!< SCB CFSR (UFSR): INVSTATE Mask */

#define SCB_CFSR_UNDEFINSTR_Pos           (SCB_CFSR_USGFAULTSR_Pos + 0U)                  /*!< SCB CFSR (UFSR): UNDEFINSTR Position */
#define SCB_CFSR_UNDEFINSTR_Msk           (1UL << SCB_CFSR_UNDEFINSTR_Pos)                /*!< SCB CFSR (UFSR): UNDEFINSTR Mask */

/* SCB Hard Fault Status Register Definitions */
#define SCB_HFSR_DEBUGEVT_Pos              31U                                            /*!< SCB HFSR: DEBUGEVT Position */
#define SCB_HFSR_DEBUGEVT_Msk              (1UL << SCB_HFSR_DEBUGEVT_Pos)                 /*!< SCB HFSR: DEBUGEVT Mask */

#define SCB_HFSR_FORCED_Pos                30U                                            /*!< SCB HFSR: FORCED Position */
#define SCB_HFSR_FORCED_Msk                (1UL << SCB_HFSR_FORCED_Pos)                   /*!< SCB HFSR: FORCED Mask */

#define SCB_HFSR_VECTTBL_Pos                1U                                            /*!< SCB HFSR: VECTTBL Position */
#define SCB_HFSR_VECTTBL_Msk               (1UL << SCB_HFSR_VECTTBL_Pos)                  /*!< SCB HFSR: VECTTBL Mask */

/* SCB Debug Fault Status Register Definitions */
#define SCB_DFSR_PMU_Pos                    5U                                            /*!< SCB DFSR: PMU Position */
#define SCB_DFSR_PMU_Msk                   (1UL << SCB_DFSR_PMU_Pos)                      /*!< SCB DFSR: PMU Mask */

#define SCB_DFSR_EXTERNAL_Pos               4U                                            /*!< SCB DFSR: EXTERNAL Position */
#define SCB_DFSR_EXTERNAL_Msk              (1UL << SCB_DFSR_EXTERNAL_Pos)                 /*!< SCB DFSR: EXTERNAL Mask */

#define SCB_DFSR_VCATCH_Pos                 3U                                            /*!< SCB DFSR: VCATCH Position */
#define SCB_DFSR_VCATCH_Msk                (1UL << SCB_DFSR_VCATCH_Pos)                   /*!< SCB DFSR: VCATCH Mask */

#define SCB_DFSR_DWTTRAP_Pos                2U                                            /*!< SCB DFSR: DWTTRAP Position */
#define SCB_DFSR_DWTTRAP_Msk               (1UL << SCB_DFSR_DWTTRAP_Pos)                  /*!< SCB DFSR: DWTTRAP Mask */

#define SCB_DFSR_BKPT_Pos                   1U                                            /*!< SCB DFSR: BKPT Position */
#define SCB_DFSR_BKPT_Msk                  (1UL << SCB_DFSR_BKPT_Pos)                     /*!< SCB DFSR: BKPT Mask */

#define SCB_DFSR_HALTED_Pos                 0U                                            /*!< SCB DFSR: HALTED Position */
#define SCB_DFSR_HALTED_Msk                (1UL /*<< SCB_DFSR_HALTED_Pos*/)               /*!< SCB DFSR: HALTED Mask */

/* SCB Non-Secure Access Control Register Definitions */
#define SCB_NSACR_CP11_Pos                 11U                                            /*!< SCB NSACR: CP11 Position */
#define SCB_NSACR_CP11_Msk                 (1UL << SCB_NSACR_CP11_Pos)                    /*!< SCB NSACR: CP11 Mask */

#define SCB_NSACR_CP10_Pos                 10U                                            /*!< SCB NSACR: CP10 Position */
#define SCB_NSACR_CP10_Msk                 (1UL << SCB_NSACR_CP10_Pos)                    /*!< SCB NSACR: CP10 Mask */

#define SCB_NSACR_CP7_Pos                   7U                                            /*!< SCB NSACR: CP7 Position */
#define SCB_NSACR_CP7_Msk                  (1UL << SCB_NSACR_CP7_Pos)                     /*!< SCB NSACR: CP7 Mask */

#define SCB_NSACR_CP6_Pos                   6U                                            /*!< SCB NSACR: CP6 Position */
#define SCB_NSACR_CP6_Msk                  (1UL << SCB_NSACR_CP6_Pos)                     /*!< SCB NSACR: CP6 Mask */

#define SCB_NSACR_CP5_Pos                   5U                                            /*!< SCB NSACR: CP5 Position */
#define SCB_NSACR_CP5_Msk                  (1UL << SCB_NSACR_CP5_Pos)                     /*!< SCB NSACR: CP5 Mask */

#define SCB_NSACR_CP4_Pos                   4U                                            /*!< SCB NSACR: CP4 Position */
#define SCB_NSACR_CP4_Msk                  (1UL << SCB_NSACR_CP4_Pos)                     /*!< SCB NSACR: CP4 Mask */

#define SCB_NSACR_CP3_Pos                   3U                                            /*!< SCB NSACR: CP3 Position */
#define SCB_NSACR_CP3_Msk                  (1UL << SCB_NSACR_CP3_Pos)                     /*!< SCB NSACR: CP3 Mask */

#define SCB_NSACR_CP2_Pos                   2U                                            /*!< SCB NSACR: CP2 Position */
#define SCB_NSACR_CP2_Msk                  (1UL << SCB_NSACR_CP2_Pos)                     /*!< SCB NSACR: CP2 Mask */

#define SCB_NSACR_CP1_Pos                   1U                                            /*!< SCB NSACR: CP1 Position */
#define SCB_NSACR_CP1_Msk                  (1UL << SCB_NSACR_CP1_Pos)                     /*!< SCB NSACR: CP1 Mask */

#define SCB_NSACR_CP0_Pos                   0U                                            /*!< SCB NSACR: CP0 Position */
#define SCB_NSACR_CP0_Msk                  (1UL /*<< SCB_NSACR_CP0_Pos*/)                 /*!< SCB NSACR: CP0 Mask */

/* SCB Debug Feature Register 0 Definitions */
#define SCB_ID_DFR_UDE_Pos                 28U                                            /*!< SCB ID_DFR: UDE Position */
#define SCB_ID_DFR_UDE_Msk                 (0xFUL << SCB_ID_DFR_UDE_Pos)                  /*!< SCB ID_DFR: UDE Mask */

#define SCB_ID_DFR_MProfDbg_Pos            20U                                            /*!< SCB ID_DFR: MProfDbg Position */
#define SCB_ID_DFR_MProfDbg_Msk            (0xFUL << SCB_ID_DFR_MProfDbg_Pos)             /*!< SCB ID_DFR: MProfDbg Mask */

/* SCB Cache Level ID Register Definitions */
#define SCB_CLIDR_LOUU_Pos                 27U                                            /*!< SCB CLIDR: LoUU Position */
#define SCB_CLIDR_LOUU_Msk                 (7UL << SCB_CLIDR_LOUU_Pos)                    /*!< SCB CLIDR: LoUU Mask */

#define SCB_CLIDR_LOC_Pos                  24U                                            /*!< SCB CLIDR: LoC Position */
#define SCB_CLIDR_LOC_Msk                  (7UL << SCB_CLIDR_LOC_Pos)                     /*!< SCB CLIDR: LoC Mask */

/* SCB Cache Type Register Definitions */
#define SCB_CTR_FORMAT_Pos                 29U                                            /*!< SCB CTR: Format Position */
#define SCB_CTR_FORMAT_Msk                 (7UL << SCB_CTR_FORMAT_Pos)                    /*!< SCB CTR: Format Mask */

#define SCB_CTR_CWG_Pos                    24U                                            /*!< SCB CTR: CWG Position */
#define SCB_CTR_CWG_Msk                    (0xFUL << SCB_CTR_CWG_Pos)                     /*!< SCB CTR: CWG Mask */

#define SCB_CTR_ERG_Pos                    20U                                            /*!< SCB CTR: ERG Position */
#define SCB_CTR_ERG_Msk                    (0xFUL << SCB_CTR_ERG_Pos)                     /*!< SCB CTR: ERG Mask */

#define SCB_CTR_DMINLINE_Pos               16U                                            /*!< SCB CTR: DminLine Position */
#define SCB_CTR_DMINLINE_Msk               (0xFUL << SCB_CTR_DMINLINE_Pos)                /*!< SCB CTR: DminLine Mask */

#define SCB_CTR_IMINLINE_Pos                0U                                            /*!< SCB CTR: ImInLine Position */
#define SCB_CTR_IMINLINE_Msk               (0xFUL /*<< SCB_CTR_IMINLINE_Pos*/)            /*!< SCB CTR: ImInLine Mask */

/* SCB Cache Size ID Register Definitions */
#define SCB_CCSIDR_WT_Pos                  31U                                            /*!< SCB CCSIDR: WT Position */
#define SCB_CCSIDR_WT_Msk                  (1UL << SCB_CCSIDR_WT_Pos)                     /*!< SCB CCSIDR: WT Mask */

#define SCB_CCSIDR_WB_Pos                  30U                                            /*!< SCB CCSIDR: WB Position */
#define SCB_CCSIDR_WB_Msk                  (1UL << SCB_CCSIDR_WB_Pos)                     /*!< SCB CCSIDR: WB Mask */

#define SCB_CCSIDR_RA_Pos                  29U                                            /*!< SCB CCSIDR: RA Position */
#define SCB_CCSIDR_RA_Msk                  (1UL << SCB_CCSIDR_RA_Pos)                     /*!< SCB CCSIDR: RA Mask */

#define SCB_CCSIDR_WA_Pos                  28U                                            /*!< SCB CCSIDR: WA Position */
#define SCB_CCSIDR_WA_Msk                  (1UL << SCB_CCSIDR_WA_Pos)                     /*!< SCB CCSIDR: WA Mask */

#define SCB_CCSIDR_NUMSETS_Pos             13U                                            /*!< SCB CCSIDR: NumSets Position */
#define SCB_CCSIDR_NUMSETS_Msk             (0x7FFFUL << SCB_CCSIDR_NUMSETS_Pos)           /*!< SCB CCSIDR: NumSets Mask */

#define SCB_CCSIDR_ASSOCIATIVITY_Pos        3U                                            /*!< SCB CCSIDR: Associativity Position */
#define SCB_CCSIDR_ASSOCIATIVITY_Msk       (0x3FFUL << SCB_CCSIDR_ASSOCIATIVITY_Pos)      /*!< SCB CCSIDR: Associativity Mask */

#define SCB_CCSIDR_LINESIZE_Pos             0U                                            /*!< SCB CCSIDR: LineSize Position */
#define SCB_CCSIDR_LINESIZE_Msk            (7UL /*<< SCB_CCSIDR_LINESIZE_Pos*/)           /*!< SCB CCSIDR: LineSize Mask */

/* SCB Cache Size Selection Register Definitions */
#define SCB_CSSELR_LEVEL_Pos                1U                                            /*!< SCB CSSELR: Level Position */
#define SCB_CSSELR_LEVEL_Msk               (7UL << SCB_CSSELR_LEVEL_Pos)                  /*!< SCB CSSELR: Level Mask */

#define SCB_CSSELR_IND_Pos                  0U                                            /*!< SCB CSSELR: InD Position */
#define SCB_CSSELR_IND_Msk                 (1UL /*<< SCB_CSSELR_IND_Pos*/)                /*!< SCB CSSELR: InD Mask */

/* SCB Software Triggered Interrupt Register Definitions */
#define SCB_STIR_INTID_Pos                  0U                                            /*!< SCB STIR: INTID Position */
#define SCB_STIR_INTID_Msk                 (0x1FFUL /*<< SCB_STIR_INTID_Pos*/)            /*!< SCB STIR: INTID Mask */

/* SCB RAS Fault Status Register Definitions */
#define SCB_RFSR_V_Pos                     31U                                            /*!< SCB RFSR: V Position */
#define SCB_RFSR_V_Msk                     (1UL << SCB_RFSR_V_Pos)                        /*!< SCB RFSR: V Mask */

#define SCB_RFSR_IS_Pos                    16U                                            /*!< SCB RFSR: IS Position */
#define SCB_RFSR_IS_Msk                    (0x7FFFUL << SCB_RFSR_IS_Pos)                  /*!< SCB RFSR: IS Mask */

#define SCB_RFSR_UET_Pos                    0U                                            /*!< SCB RFSR: UET Position */
#define SCB_RFSR_UET_Msk                   (3UL /*<< SCB_RFSR_UET_Pos*/)                  /*!< SCB RFSR: UET Mask */

/* SCB D-Cache Invalidate by Set-way Register Definitions */
#define SCB_DCISW_WAY_Pos                  30U                                            /*!< SCB DCISW: Way Position */
#define SCB_DCISW_WAY_Msk                  (3UL << SCB_DCISW_WAY_Pos)                     /*!< SCB DCISW: Way Mask */

#define SCB_DCISW_SET_Pos                   5U                                            /*!< SCB DCISW: Set Position */
#define SCB_DCISW_SET_Msk                  (0x1FFUL << SCB_DCISW_SET_Pos)                 /*!< SCB DCISW: Set Mask */

/* SCB D-Cache Clean by Set-way Register Definitions */
#define SCB_DCCSW_WAY_Pos                  30U                                            /*!< SCB DCCSW: Way Position */
#define SCB_DCCSW_WAY_Msk                  (3UL << SCB_DCCSW_WAY_Pos)                     /*!< SCB DCCSW: Way Mask */

#define SCB_DCCSW_SET_Pos                   5U                                            /*!< SCB DCCSW: Set Position */
#define SCB_DCCSW_SET_Msk                  (0x1FFUL << SCB_DCCSW_SET_Pos)                 /*!< SCB DCCSW: Set Mask */

/* SCB D-Cache Clean and Invalidate by Set-way Register Definitions */
#define SCB_DCCISW_WAY_Pos                 30U                                            /*!< SCB DCCISW: Way Position */
#define SCB_DCCISW_WAY_Msk                 (3UL << SCB_DCCISW_WAY_Pos)                    /*!< SCB DCCISW: Way Mask */

#define SCB_DCCISW_SET_Pos                  5U                                            /*!< SCB DCCISW: Set Position */
#define SCB_DCCISW_SET_Msk                 (0x1FFUL << SCB_DCCISW_SET_Pos)                /*!< SCB DCCISW: Set Mask */

/*@} end of group CMSIS_SCB */


/**
  \ingroup  CMSIS_core_register
  \defgroup CMSIS_SCnSCB System Controls not in SCB (SCnSCB)
  \brief    Type definitions for the System Control and ID Register not in the SCB
  @{
 */

/**
  \brief  Structure type to access the System Control and ID Register not in the SCB.
 */
typedef struct
{
        uint32_t RESERVED0[1U];
  __IM  uint32_t ICTR;                   /*!< Offset: 0x004 (R/ )  Interrupt Controller Type Register */
  __IOM uint32_t ACTLR;                  /*!< Offset: 0x008 (R/W)  Auxiliary Control Register */
  __IOM uint32_t CPPWR;                  /*!< Offset: 0x00C (R/W)  Coprocessor Power Control  Register */
} SCnSCB_Type;

/* Interrupt Controller Type Register Definitions */
#define SCnSCB_ICTR_INTLINESNUM_Pos         0U                                         /*!< ICTR: INTLINESNUM Position */
#define SCnSCB_ICTR_INTLINESNUM_Msk        (0xFUL /*<< SCnSCB_ICTR_INTLINESNUM_Pos*/)  /*!< ICTR: INTLINESNUM Mask */

/*@} end of group CMSIS_SCnotSCB */


/**
  \ingroup  CMSIS_core_register
  \defgroup CMSIS_SysTick     System Tick Timer (SysTick)
  \brief    Type definitions for the System Timer Registers.
  @{
 */

/**
  \brief  Structure type to access the System Timer (SysTick).
 */
typedef struct
{
  __IOM uint32_t CTRL;                   /*!< Offset: 0x000 (R/W)  SysTick Control and Status Register */
  __IOM uint32_t LOAD;                   /*!< Offset: 0x004 (R/W)  SysTick Reload Value Register */
  __IOM uint32_t VAL;                    /*!< Offset: 0x008 (R/W)  SysTick Current Value Register */
  __IM  uint32_t CALIB;                  /*!< Offset: 0x00C (R/ )  SysTick Calibration Register */
} SysTick_Type;

/* SysTick Control / Status Register Definitions */
#define SysTick_CTRL_COUNTFLAG_Pos         16U                                            /*!< SysTick CTRL: COUNTFLAG Position */
#define SysTick_CTRL_COUNTFLAG_Msk         (1UL << SysTick_CTRL_COUNTFLAG_Pos)            /*!< SysTick CTRL: COUNTFLAG Mask */

#define SysTick_CTRL_CLKSOURCE_Pos          2U                                            /*!< SysTick CTRL: CLKSOURCE Position */
#define SysTick_CTRL_CLKSOURCE_Msk         (1UL << SysTick_CTRL_CLKSOURCE_Pos)            /*!< SysTick CTRL: CLKSOURCE Mask */

#define SysTick_CTRL_TICKINT_Pos            1U                                            /*!< SysTick CTRL: TICKINT Position */
#define SysTick_CTRL_TICKINT_Msk           (1UL << SysTick_CTRL_TICKINT_Pos)              /*!< SysTick CTRL: TICKINT Mask */

#define SysTick_CTRL_ENABLE_Pos             0U                                            /*!< SysTick CTRL: ENABLE Position */
#define SysTick_CTRL_ENABLE_Msk            (1UL /*<< SysTick_CTRL_ENABLE_Pos*/)           /*!< SysTick CTRL: ENABLE Mask */

/* SysTick Reload Register Definitions */
#define SysTick_LOAD_RELOAD_Pos             0U                                            /*!< SysTick LOAD: RELOAD Position */
#define SysTick_LOAD_RELOAD_Msk            (0xFFFFFFUL /*<< SysTick_LOAD_RELOAD_Pos*/)    /*!< SysTick LOAD: RELOAD Mask */

/* SysTick Current Register Definitions */
#define SysTick_VAL_CURRENT_Pos             0U                                            /*!< SysTick VAL: CURRENT Position */
#define SysTick_VAL_CURRENT_Msk            (0xFFFFFFUL /*<< SysTick_VAL_CURRENT_Pos*/)    /*!< SysTick VAL: CURRENT Mask */

/* SysTick Calibration Register Definitions */
#define SysTick_CALIB_NOREF_Pos            31U                                            /*!< SysTick CALIB: NOREF Position */
#define SysTick_CALIB_NOREF_Msk            (1UL << SysTick_CALIB_NOREF_Pos)               /*!< SysTick CALIB: NOREF Mask */

#define SysTick_CALIB_SKEW_Pos             30U                                            /*!< SysTick CALIB: SKEW Position */
#define SysTick_CALIB_SKEW_Msk             (1UL << SysTick_CALIB_SKEW_Pos)                /*!< SysTick CALIB: SKEW Mask */

#define SysTick_CALIB_TENMS_Pos             0U                                            /*!< SysTick CALIB: TENMS Position */
#define SysTick_CALIB_TENMS_Msk            (0xFFFFFFUL /*<< SysTick_CALIB_TENMS_Pos*/)    /*!< SysTick CALIB: TENMS Mask */

/*@} end of group CMSIS_SysTick */


/**
  \ingroup  CMSIS_core_register
  \defgroup CMSIS_ITM     Instrumentation Trace Macrocell (ITM)
  \brief    Type definitions for the Instrumentation Trace Macrocell (ITM)
  @{
 */

/**
  \brief  Structure type to access the Instrumentation Trace Macrocell Register (ITM).
 */
typedef struct
{
  __OM  union
  {
    __OM  uint8_t    u8;                 /*!< Offset: 0x000 ( /W)  ITM Stimulus Port 8-bit */
    __OM  uint16_t   u16;                /*!< Offset: 0x000 ( /W)  ITM Stimulus Port 16-bit */
    __OM  uint32_t   u32;                /*!< Offset: 0x000 ( /W)  ITM Stimulus Port 32-bit */
  }  PORT [32U];                         /*!< Offset: 0x000 ( /W)  ITM Stimulus Port Registers */
        uint32_t RESERVED0[864U];
  __IOM uint32_t TER;                    /*!< Offset: 0xE00 (R/W)  ITM Trace Enable Register */
        uint32_t RESERVED1[15U];
  __IOM uint32_t TPR;                    /*!< Offset: 0xE40 (R/W)  ITM Trace Privilege Register */
        uint32_t RESERVED2[15U];
  __IOM uint32_t TCR;                    /*!< Offset: 0xE80 (R/W)  ITM Trace Control Register */
        uint32_t RESERVED3[32U];
        uint32_t RESERVED4[43U];
  __OM  uint32_t LAR;                    /*!< Offset: 0xFB0 ( /W)  ITM Lock Access Register */
  __IM  uint32_t LSR;                    /*!< Offset: 0xFB4 (R/ )  ITM Lock Status Register */
        uint32_t RESERVED5[1U];
  __IM  uint32_t DEVARCH;                /*!< Offset: 0xFBC (R/ )  ITM Device Architecture Register */
        uint32_t RESERVED6[3U];
  __IM  uint32_t DEVTYPE;                /*!< Offset: 0xFCC (R/ )  ITM Device Type Register */
  __IM  uint32_t PID4;                   /*!< Offset: 0xFD0 (R/ )  ITM Peripheral Identification Register #4 */
  __IM  uint32_t PID5;                   /*!< Offset: 0xFD4 (R/ )  ITM Peripheral Identification Register #5 */
  __IM  uint32_t PID6;                   /*!< Offset: 0xFD8 (R/ )  ITM Peripheral Identification Register #6 */
  __IM  uint32_t PID7;                   /*!< Offset: 0xFDC (R/ )  ITM Peripheral Identification Register #7 */
  __IM  uint32_t PID0;                   /*!< Offset: 0xFE0 (R/ )  ITM Peripheral Identification Register #0 */
  __IM  uint32_t PID1;                   /*!< Offset: 0xFE4 (R/ )  ITM Peripheral Identification Register #1 */
  __IM  uint32_t PID2;                   /*!< Offset: 0xFE8 (R/ )  ITM Peripheral Identification Register #2 */
  __IM  uint32_t PID3;                   /*!< Offset: 0xFEC (R/ )  ITM Peripheral Identification Register #3 */
  __IM  uint32_t CID0;                   /*!< Offset: 0xFF0 (R/ )  ITM Component  Identification Register #0 */
  __IM  uint32_t CID1;                   /*!< Offset: 0xFF4 (R/ )  ITM Component  Identification Register #1 */
  __IM  uint32_t CID2;                   /*!< Offset: 0xFF8 (R/ )  ITM Component  Identification Register #2 */
  __IM  uint32_t CID3;                   /*!< Offset: 0xFFC (R/ )  ITM Component  Identification Register #3 */
} ITM_Type;

/* ITM Stimulus Port Register Definitions */
#define ITM_STIM_DISABLED_Pos               1U                                            /*!< ITM STIM: DISABLED Position */
#define ITM_STIM_DISABLED_Msk              (0x1UL << ITM_STIM_DISABLED_Pos)               /*!< ITM STIM: DISABLED Mask */

#define ITM_STIM_FIFOREADY_Pos              0U                                            /*!< ITM STIM: FIFOREADY Position */
#define ITM_STIM_FIFOREADY_Msk             (0x1UL /*<< ITM_STIM_FIFOREADY_Pos*/)          /*!< ITM STIM: FIFOREADY Mask */

/* ITM Trace Privilege Register Definitions */
#define ITM_TPR_PRIVMASK_Pos                0U                                            /*!< ITM TPR: PRIVMASK Position */
#define ITM_TPR_PRIVMASK_Msk               (0xFUL /*<< ITM_TPR_PRIVMASK_Pos*/)            /*!< ITM TPR: PRIVMASK Mask */

/* ITM Trace Control Register Definitions */
#define ITM_TCR_BUSY_Pos                   23U                                            /*!< ITM TCR: BUSY Position */
#define ITM_TCR_BUSY_Msk                   (1UL << ITM_TCR_BUSY_Pos)                      /*!< ITM TCR: BUSY Mask */

#define ITM_TCR_TRACEBUSID_Pos             16U                                            /*!< ITM TCR: ATBID Position */
#define ITM_TCR_TRACEBUSID_Msk             (0x7FUL << ITM_TCR_TRACEBUSID_Pos)             /*!< ITM TCR: ATBID Mask */

#define ITM_TCR_GTSFREQ_Pos                10U                                            /*!< ITM TCR: Global timestamp frequency Position */
#define ITM_TCR_GTSFREQ_Msk                (3UL << ITM_TCR_GTSFREQ_Pos)                   /*!< ITM TCR: Global timestamp frequency Mask */

#define ITM_TCR_TSPRESCALE_Pos              8U                                            /*!< ITM TCR: TSPRESCALE Position */
#define ITM_TCR_TSPRESCALE_Msk             (3UL << ITM_TCR_TSPRESCALE_Pos)                /*!< ITM TCR: TSPRESCALE Mask */

#define ITM_TCR_STALLENA_Pos                5U                                            /*!< ITM TCR: STALLENA Position */
#define ITM_TCR_STALLENA_Msk               (1UL << ITM_TCR_STALLENA_Pos)                  /*!< ITM TCR: STALLENA Mask */

#define ITM_TCR_SWOENA_Pos                  4U                                            /*!< ITM TCR: SWOENA Position */
#define ITM_TCR_SWOENA_Msk                 (1UL << ITM_TCR_SWOENA_Pos)                    /*!< ITM TCR: SWOENA Mask */

#define ITM_TCR_DWTENA_Pos                  3U                                            /*!< ITM TCR: DWTENA Position */
#define ITM_TCR_DWTENA_Msk                 (1UL << ITM_TCR_DWTENA_Pos)                    /*!< ITM TCR: DWTENA Mask */

#define ITM_TCR_SYNCENA_Pos                 2U                                            /*!< ITM TCR: SYNCENA Position */
#define ITM_TCR_SYNCENA_Msk                (1UL << ITM_TCR_SYNCENA_Pos)                   /*!< ITM TCR: SYNCENA Mask */

#define ITM_TCR_TSENA_Pos                   1U                                            /*!< ITM TCR: TSENA Position */
#define ITM_TCR_TSENA_Msk                  (1UL << ITM_TCR_TSENA_Pos)                     /*!< ITM TCR: TSENA Mask */

#define ITM_TCR_ITMENA_Pos                  0U                                            /*!< ITM TCR: ITM Enable bit Position */
#define ITM_TCR_ITMENA_Msk                 (1UL /*<< ITM_TCR_ITMENA_Pos*/)                /*!< ITM TCR: ITM Enable bit Mask */

/* ITM Lock Status Register Definitions */
#define ITM_LSR_ByteAcc_Pos                 2U                                            /*!< ITM LSR: ByteAcc Position */
#define ITM_LSR_ByteAcc_Msk                (1UL << ITM_LSR_ByteAcc_Pos)                   /*!< ITM LSR: ByteAcc Mask */

#define ITM_LSR_Access_Pos                  1U                                            /*!< ITM LSR: Access Position */
#define ITM_LSR_Access_Msk                 (1UL << ITM_LSR_Access_Pos)                    /*!< ITM LSR: Access Mask */

#define ITM_LSR_Present_Pos                 0U                                            /*!< ITM LSR: Present Position */
#define ITM_LSR_Present_Msk                (1UL /*<< ITM_LSR_Present_Pos*/)               /*!< ITM LSR: Present Mask */

/*@}*/ /* end of group CMSIS_ITM */


/**
  \ingroup  CMSIS_core_register
  \defgroup CMSIS_DWT     Data Watchpoint and Trace (DWT)
  \brief    Type definitions for the Data Watchpoint and Trace (DWT)
  @{
 */

/**
  \brief  Structure type to access the Data Watchpoint and Trace Register (DWT).
 */
typedef struct
{
  __IOM uint32_t CTRL;                   /*!< Offset: 0x000 (R/W)  Control Register */
  __IOM uint32_t CYCCNT;                 /*!< Offset: 0x004 (R/W)  Cycle Count Register */
  __IOM uint32_t CPICNT;                 /*!< Offset: 0x008 (R/W)  CPI Count Register */
  __IOM uint32_t EXCCNT;                 /*!< Offset: 0x00C (R/W)  Exception Overhead Count Register */
  __IOM uint32_t SLEEPCNT;               /*!< Offset: 0x010 (R/W)  Sleep Count Register */
  __IOM uint32_t LSUCNT;                 /*!< Offset: 0x014 (R/W)  LSU Count Register */
  __IOM uint32_t FOLDCNT;                /*!< Offset: 0x018 (R/W)  Folded-instruction Count Register */
  __IM  uint32_t PCSR;                   /*!< Offset: 0x01C (R/ )  Program Counter Sample Register */
  __IOM uint32_t COMP0;                  /*!< Offset: 0x020 (R/W)  Comparator Register 0 */
        uint32_t RESERVED1[1U];
  __IOM uint32_t FUNCTION0;              /*!< Offset: 0x028 (R/W)  Function Register 0 */
        uint32_t RESERVED2[1U];
  __IOM uint32_t COMP1;                  /*!< Offset: 0x030 (R/W)  Comparator Register 1 */
        uint32_t RESERVED3[1U];
  __IOM uint32_t FUNCTION1;              /*!< Offset: 0x038 (R/W)  Function Register 1 */
        uint32_t RESERVED4[1U];
  __IOM uint32_t COMP2;                  /*!< Offset: 0x040 (R/W)  Comparator Register 2 */
        uint32_t RESERVED5[1U];
  __IOM uint32_t FUNCTION2;              /*!< Offset: 0x048 (R/W)  Function Register 2 */
        uint32_t RESERVED6[1U];
  __IOM uint32_t COMP3;                  /*!< Offset: 0x050 (R/W)  Comparator Register 3 */
        uint32_t RESERVED7[1U];
  __IOM uint32_t FUNCTION3;              /*!< Offset: 0x058 (R/W)  Function Register 3 */
        uint32_t RESERVED8[1U];
  __IOM uint32_t COMP4;                  /*!< Offset: 0x060 (R/W)  Comparator Register 4 */
        uint32_t RESERVED9[1U];
  __IOM uint32_t FUNCTION4;              /*!< Offset: 0x068 (R/W)  Function Register 4 */
        uint32_t RESERVED10[1U];
  __IOM uint32_t COMP5;                  /*!< Offset: 0x070 (R/W)  Comparator Register 5 */
        uint32_t RESERVED11[1U];
  __IOM uint32_t FUNCTION5;              /*!< Offset: 0x078 (R/W)  Function Register 5 */
        uint32_t RESERVED12[1U];
  __IOM uint32_t COMP6;                  /*!< Offset: 0x080 (R/W)  Comparator Register 6 */
        uint32_t RESERVED13[1U];
  __IOM uint32_t FUNCTION6;              /*!< Offset: 0x088 (R/W)  Function Register 6 */
        uint32_t RESERVED14[1U];
  __IOM uint32_t COMP7;                  /*!< Offset: 0x090 (R/W)  Comparator Register 7 */
        uint32_t RESERVED15[1U];
  __IOM uint32_t FUNCTION7;              /*!< Offset: 0x098 (R/W)  Function Register 7 */
        uint32_t RESERVED16[1U];
  __IOM uint32_t COMP8;                  /*!< Offset: 0x0A0 (R/W)  Comparator Register 8 */
        uint32_t RESERVED17[1U];
  __IOM uint32_t FUNCTION8;              /*!< Offset: 0x0A8 (R/W)  Function Register 8 */
        uint32_t RESERVED18[1U];
  __IOM uint32_t COMP9;                  /*!< Offset: 0x0B0 (R/W)  Comparator Register 9 */
        uint32_t RESERVED19[1U];
  __IOM uint32_t FUNCTION9;              /*!< Offset: 0x0B8 (R/W)  Function Register 9 */
        uint32_t RESERVED20[1U];
  __IOM uint32_t COMP10;                 /*!< Offset: 0x0C0 (R/W)  Comparator Register 10 */
        uint32_t RESERVED21[1U];
  __IOM uint32_t FUNCTION10;             /*!< Offset: 0x0C8 (R/W)  Function Register 10 */
        uint32_t RESERVED22[1U];
  __IOM uint32_t COMP11;                 /*!< Offset: 0x0D0 (R/W)  Comparator Register 11 */
        uint32_t RESERVED23[1U];
  __IOM uint32_t FUNCTION11;             /*!< Offset: 0x0D8 (R/W)  Function Register 11 */
        uint32_t RESERVED24[1U];
  __IOM uint32_t COMP12;                 /*!< Offset: 0x0E0 (R/W)  Comparator Register 12 */
        uint32_t RESERVED25[1U];
  __IOM uint32_t FUNCTION12;             /*!< Offset: 0x0E8 (R/W)  Function Register 12 */
        uint32_t RESERVED26[1U];
  __IOM uint32_t COMP13;                 /*!< Offset: 0x0F0 (R/W)  Comparator Register 13 */
        uint32_t RESERVED27[1U];
  __IOM uint32_t FUNCTION13;             /*!< Offset: 0x0F8 (R/W)  Function Register 13 */
        uint32_t RESERVED28[1U];
  __IOM uint32_t COMP14;                 /*!< Offset: 0x100 (R/W)  Comparator Register 14 */
        uint32_t RESERVED29[1U];
  __IOM uint32_t FUNCTION14;             /*!< Offset: 0x108 (R/W)  Function Register 14 */
        uint32_t RESERVED30[1U];
  __IOM uint32_t COMP15;                 /*!< Offset: 0x110 (R/W)  Comparator Register 15 */
        uint32_t RESERVED31[1U];
  __IOM uint32_t FUNCTION15;             /*!< Offset: 0x118 (R/W)  Function Register 15 */
        uint32_t RESERVED32[934U];
  __IM  uint32_t LSR;                    /*!< Offset: 0xFB4 (R  )  Lock Status Register */
        uint32_t RESERVED33[1U];
  __IM  uint32_t DEVARCH;                /*!< Offset: 0xFBC (R/ )  Device Architecture Register */
} DWT_Type;

/* DWT Control Register Definitions */
#define DWT_CTRL_NUMCOMP_Pos               28U                                         /*!< DWT CTRL: NUMCOMP Position */
#define DWT_CTRL_NUMCOMP_Msk               (0xFUL << DWT_CTRL_NUMCOMP_Pos)             /*!< DWT CTRL: NUMCOMP Mask */

#define DWT_CTRL_NOTRCPKT_Pos              27U                                         /*!< DWT CTRL: NOTRCPKT Position */
#define DWT_CTRL_NOTRCPKT_Msk              (0x1UL << DWT_CTRL_NOTRCPKT_Pos)            /*!< DWT CTRL: NOTRCPKT Mask */

#define DWT_CTRL_NOEXTTRIG_Pos             26U                                         /*!< DWT CTRL: NOEXTTRIG Position */
#define DWT_CTRL_NOEXTTRIG_Msk             (0x1UL << DWT_CTRL_NOEXTTRIG_Pos)           /*!< DWT CTRL: NOEXTTRIG Mask */

#define DWT_CTRL_NOCYCCNT_Pos              25U                                         /*!< DWT CTRL: NOCYCCNT Position */
#define DWT_CTRL_NOCYCCNT_Msk              (0x1UL << DWT_CTRL_NOCYCCNT_Pos)            /*!< DWT CTRL: NOCYCCNT Mask */

#define DWT_CTRL_NOPRFCNT_Pos              24U                                         /*!< DWT CTRL: NOPRFCNT Position */
#define DWT_CTRL_NOPRFCNT_Msk              (0x1UL << DWT_CTRL_NOPRFCNT_Pos)            /*!< DWT CTRL: NOPRFCNT Mask */

#define DWT_CTRL_CYCDISS_Pos               23U                                         /*!< DWT CTRL: CYCDISS Position */
#define DWT_CTRL_CYCDISS_Msk               (0x1UL << DWT_CTRL_CYCDISS_Pos)             /*!< DWT CTRL: CYCDISS Mask */

#define DWT_CTRL_CYCEVTENA_Pos             22U                                         /*!< DWT CTRL: CYCEVTENA Position */
#define DWT_CTRL_CYCEVTENA_Msk             (0x1UL << DWT_CTRL_CYCEVTENA_Pos)           /*!< DWT CTRL: CYCEVTENA Mask */

#define DWT_CTRL_FOLDEVTENA_Pos            21U                                         /*!< DWT CTRL: FOLDEVTENA Position */
#define DWT_CTRL_FOLDEVTENA_Msk            (0x1UL << DWT_CTRL_FOLDEVTENA_Pos)          /*!< DWT CTRL: FOLDEVTENA Mask */

#define DWT_CTRL_LSUEVTENA_Pos             20U                                         /*!< DWT CTRL: LSUEVTENA Position */
#define DWT_CTRL_LSUEVTENA_Msk             (0x1UL << DWT_CTRL_LSUEVTENA_Pos)           /*!< DWT CTRL: LSUEVTENA Mask */

#define DWT_CTRL_SLEEPEVTENA_Pos           19U                                         /*!< DWT CTRL: SLEEPEVTENA Position */
#define DWT_CTRL_SLEEPEVTENA_Msk           (0x1UL << DWT_CTRL_SLEEPEVTENA_Pos)         /*!< DWT CTRL: SLEEPEVTENA Mask */

#define DWT_CTRL_EXCEVTENA_Pos             18U                                         /*!< DWT CTRL: EXCEVTENA Position */
#define DWT_CTRL_EXCEVTENA_Msk             (0x1UL << DWT_CTRL_EXCEVTENA_Pos)           /*!< DWT CTRL: EXCEVTENA Mask */

#define DWT_CTRL_CPIEVTENA_Pos             17U                                         /*!< DWT CTRL: CPIEVTENA Position */
#define DWT_CTRL_CPIEVTENA_Msk             (0x1UL << DWT_CTRL_CPIEVTENA_Pos)           /*!< DWT CTRL: CPIEVTENA Mask */

#define DWT_CTRL_EXCTRCENA_Pos             16U                                         /*!< DWT CTRL: EXCTRCENA Position */
#define DWT_CTRL_EXCTRCENA_Msk             (0x1UL << DWT_CTRL_EXCTRCENA_Pos)           /*!< DWT CTRL: EXCTRCENA Mask */

#define DWT_CTRL_PCSAMPLENA_Pos            12U                                         /*!< DWT CTRL: PCSAMPLENA Position */
#define DWT_CTRL_PCSAMPLENA_Msk            (0x1UL << DWT_CTRL_PCSAMPLENA_Pos)          /*!< DWT CTRL: PCSAMPLENA Mask */

#define DWT_CTRL_SYNCTAP_Pos               10U                                         /*!< DWT CTRL: SYNCTAP Position */
#define DWT_CTRL_SYNCTAP_Msk               (0x3UL << DWT_CTRL_SYNCTAP_Pos)             /*!< DWT CTRL: SYNCTAP Mask */

#define DWT_CTRL_CYCTAP_Pos                 9U                                         /*!< DWT CTRL: CYCTAP Position */
#define DWT_CTRL_CYCTAP_Msk                (0x1UL << DWT_CTRL_CYCTAP_Pos)              /*!< DWT CTRL: CYCTAP Mask */

#define DWT_CTRL_POSTINIT_Pos               5U                                         /*!< DWT CTRL: POSTINIT Position */
#define DWT_CTRL_POSTINIT_Msk              (0xFUL << DWT_CTRL_POSTINIT_Pos)            /*!< DWT CTRL: POSTINIT Mask */

#define DWT_CTRL_POSTPRESET_Pos             1U                                         /*!< DWT CTRL: POSTPRESET Position */
#define DWT_CTRL_POSTPRESET_Msk            (0xFUL << DWT_CTRL_POSTPRESET_Pos)          /*!< DWT CTRL: POSTPRESET Mask */

#define DWT_CTRL_CYCCNTENA_Pos              0U                                         /*!< DWT CTRL: CYCCNTENA Position */
#define DWT_CTRL_CYCCNTENA_Msk             (0x1UL /*<< DWT_CTRL_CYCCNTENA_Pos*/)       /*!< DWT CTRL: CYCCNTENA Mask */

/* DWT CPI Count Register Definitions */
#define DWT_CPICNT_CPICNT_Pos               0U                                         /*!< DWT CPICNT: CPICNT Position */
#define DWT_CPICNT_CPICNT_Msk              (0xFFUL /*<< DWT_CPICNT_CPICNT_Pos*/)       /*!< DWT CPICNT: CPICNT Mask */

/* DWT Exception Overhead Count Register Definitions */
#define DWT_EXCCNT_EXCCNT_Pos               0U                                         /*!< DWT EXCCNT: EXCCNT Position */
#define DWT_EXCCNT_EXCCNT_Msk              (0xFFUL /*<< DWT_EXCCNT_EXCCNT_Pos*/)       /*!< DWT EXCCNT: EXCCNT Mask */

/* DWT Sleep Count Register Definitions */
#define DWT_SLEEPCNT_SLEEPCNT_Pos           0U                                         /*!< DWT SLEEPCNT: SLEEPCNT Position */
#define DWT_SLEEPCNT_SLEEPCNT_Msk          (0xFFUL /*<< DWT_SLEEPCNT_SLEEPCNT_Pos*/)   /*!< DWT SLEEPCNT: SLEEPCNT Mask */

/* DWT LSU Count Register Definitions */
#define DWT_LSUCNT_LSUCNT_Pos               0U                                         /*!< DWT LSUCNT: LSUCNT Position */
#define DWT_LSUCNT_LSUCNT_Msk              (0xFFUL /*<< DWT_LSUCNT_LSUCNT_Pos*/)       /*!< DWT LSUCNT: LSUCNT Mask */

/* DWT Folded-instruction Count Register Definitions */
#define DWT_FOLDCNT_FOLDCNT_Pos             0U                                         /*!< DWT FOLDCNT: FOLDCNT Position */
#define DWT_FOLDCNT_FOLDCNT_Msk            (0xFFUL /*<< DWT_FOLDCNT_FOLDCNT_Pos*/)     /*!< DWT FOLDCNT: FOLDCNT Mask */

/* DWT Comparator Function Register Definitions */
#define DWT_FUNCTION_ID_Pos                27U                                         /*!< DWT FUNCTION: ID Position */
#define DWT_FUNCTION_ID_Msk                (0x1FUL << DWT_FUNCTION_ID_Pos)             /*!< DWT FUNCTION: ID Mask */

#define DWT_FUNCTION_MATCHED_Pos           24U                                         /*!< DWT FUNCTION: MATCHED Position */
#define DWT_FUNCTION_MATCHED_Msk           (0x1UL << DWT_FUNCTION_MATCHED_Pos)         /*!< DWT FUNCTION: MATCHED Mask */

#define DWT_FUNCTION_DATAVSIZE_Pos         10U                                         /*!< DWT FUNCTION: DATAVSIZE Position */
#define DWT_FUNCTION_DATAVSIZE_Msk         (0x3UL << DWT_FUNCTION_DATAVSIZE_Pos)       /*!< DWT FUNCTION: DATAVSIZE Mask */

#define DWT_FUNCTION_ACTION_Pos             4U                                         /*!< DWT FUNCTION: ACTION Position */
#define DWT_FUNCTION_ACTION_Msk            (0x1UL << DWT_FUNCTION_ACTION_Pos)          /*!< DWT FUNCTION: ACTION Mask */

#define DWT_FUNCTION_MATCH_Pos              0U                                         /*!< DWT FUNCTION: MATCH Position */
#define DWT_FUNCTION_MATCH_Msk             (0xFUL /*<< DWT_FUNCTION_MATCH_Pos*/)       /*!< DWT FUNCTION: MATCH Mask */

/*@}*/ /* end of group CMSIS_DWT */


/**
  \ingroup  CMSIS_core_register
  \defgroup CMSIS_TPI     Trace Port Interface (TPI)
  \brief    Type definitions for the Trace Port Interface (TPI)
  @{
 */

/**
  \brief  Structure type to access the Trace Port Interface Register (TPI).
 */
typedef struct
{
  __IM  uint32_t SSPSR;                  /*!< Offset: 0x000 (R/ )  Supported Parallel Port Sizes Register */
  __IOM uint32_t CSPSR;                  /*!< Offset: 0x004 (R/W)  Current Parallel Port Sizes Register */
        uint32_t RESERVED0[2U];
  __IOM uint32_t ACPR;                   /*!< Offset: 0x010 (R/W)  Asynchronous Clock Prescaler Register */
        uint32_t RESERVED1[55U];
  __IOM uint32_t SPPR;                   /*!< Offset: 0x0F0 (R/W)  Selected Pin Protocol Register */
        uint32_t RESERVED2[131U];
  __IM  uint32_t FFSR;                   /*!< Offset: 0x300 (R/ )  Formatter and Flush Status Register */
  __IOM uint32_t FFCR;                   /*!< Offset: 0x304 (R/W)  Formatter and Flush Control Register */
  __IOM uint32_t PSCR;                   /*!< Offset: 0x308 (R/W)  Periodic Synchronization Control Register */
        uint32_t RESERVED3[809U];
  __OM  uint32_t LAR;                    /*!< Offset: 0xFB0 ( /W)  Software Lock Access Register */
  __IM  uint32_t LSR;                    /*!< Offset: 0xFB4 (R/ )  Software Lock Status Register */
        uint32_t RESERVED4[4U];
  __IM  uint32_t TYPE;                   /*!< Offset: 0xFC8 (R/ )  Device Identifier Register */
  __IM  uint32_t DEVTYPE;                /*!< Offset: 0xFCC (R/ )  Device Type Register */
} TPI_Type;

/* TPI Asynchronous Clock Prescaler Register Definitions */
#define TPI_ACPR_SWOSCALER_Pos              0U                                         /*!< TPI ACPR: SWOSCALER Position */
#define TPI_ACPR_SWOSCALER_Msk             (0xFFFFUL /*<< TPI_ACPR_SWOSCALER_Pos*/)    /*!< TPI ACPR: SWOSCALER Mask */

/* TPI Selected Pin Protocol Register Definitions */
#define TPI_SPPR_TXMODE_Pos                 0U                                         /*!< TPI SPPR: TXMODE Position */
#define TPI_SPPR_TXMODE_Msk                (0x3UL /*<< TPI_SPPR_TXMODE_Pos*/)          /*!< TPI SPPR: TXMODE Mask */

/* TPI Formatter and Flush Status Register Definitions */
#define TPI_FFSR_FtNonStop_Pos              3U                                         /*!< TPI FFSR: FtNonStop Position */
#define TPI_FFSR_FtNonStop_Msk             (0x1UL << TPI_FFSR_FtNonStop_Pos)           /*!< TPI FFSR: FtNonStop Mask */

#define TPI_FFSR_TCPresent_Pos              2U                                         /*!< TPI FFSR: TCPresent Position */
#define TPI_FFSR_TCPresent_Msk             (0x1UL << TPI_FFSR_TCPresent_Pos)           /*!< TPI FFSR: TCPresent Mask */

#define TPI_FFSR_FtStopped_Pos              1U                                         /*!< TPI FFSR: FtStopped Position */
#define TPI_FFSR_FtStopped_Msk             (0x1UL << TPI_FFSR_FtStopped_Pos)           /*!< TPI FFSR: FtStopped Mask */

#define TPI_FFSR_FlInProg_Pos               0U                                         /*!< TPI FFSR: FlInProg Position */
#define TPI_FFSR_FlInProg_Msk              (0x1UL /*<< TPI_FFSR_FlInProg_Pos*/)        /*!< TPI FFSR: FlInProg Mask */

/* TPI Formatter and Flush Control Register Definitions */
#define TPI_FFCR_TrigIn_Pos                 8U                                         /*!< TPI FFCR: TrigIn Position */
#define TPI_FFCR_TrigIn_Msk                (0x1UL << TPI_FFCR_TrigIn_Pos)              /*!< TPI FFCR: TrigIn Mask */

#define TPI_FFCR_FOnMan_Pos                 6U                                         /*!< TPI FFCR: FOnMan Position */
#define TPI_FFCR_FOnMan_Msk                (0x1UL << TPI_FFCR_FOnMan_Pos)              /*!< TPI FFCR: FOnMan Mask */

#define TPI_FFCR_EnFmt_Pos                  0U                                         /*!< TPI FFCR: EnFmt Position */
#define TPI_FFCR_EnFmt_Msk                 (0x3UL << /*TPI_FFCR_EnFmt_Pos*/)           /*!< TPI FFCR: EnFmt Mask */

/* TPI Periodic Synchronization Control Register Definitions */
#define TPI_PSCR_PSCount_Pos                0U                                         /*!< TPI PSCR: PSCount Position */
#define TPI_PSCR_PSCount_Msk               (0x1FUL /*<< TPI_PSCR_PSCount_Pos*/)        /*!< TPI PSCR: TPSCount Mask */

/* TPI Software Lock Status Register Definitions */
#define TPI_LSR_nTT_Pos                     1U                                         /*!< TPI LSR: Not thirty-two bit. Position */
#define TPI_LSR_nTT_Msk                    (0x1UL << TPI_LSR_nTT_Pos)                  /*!< TPI LSR: Not thirty-two bit. Mask */

#define TPI_LSR_SLK_Pos                     1U                                         /*!< TPI LSR: Software Lock status Position */
#define TPI_LSR_SLK_Msk                    (0x1UL << TPI_LSR_SLK_Pos)                  /*!< TPI LSR: Software Lock status Mask */

#define TPI_LSR_SLI_Pos                     0U                                         /*!< TPI LSR: Software Lock implemented Position */
#define TPI_LSR_SLI_Msk                    (0x1UL /*<< TPI_LSR_SLI_Pos*/)              /*!< TPI LSR: Software Lock implemented Mask */

/* TPI DEVID Register Definitions */
#define TPI_DEVID_NRZVALID_Pos             11U                                         /*!< TPI DEVID: NRZVALID Position */
#define TPI_DEVID_NRZVALID_Msk             (0x1UL << TPI_DEVID_NRZVALID_Pos)           /*!< TPI DEVID: NRZVALID Mask */

#define TPI_DEVID_MANCVALID_Pos            10U                                         /*!< TPI DEVID: MANCVALID Position */
#define TPI_DEVID_MANCVALID_Msk            (0x1UL << TPI_DEVID_MANCVALID_Pos)          /*!< TPI DEVID: MANCVALID Mask */

#define TPI_DEVID_PTINVALID_Pos             9U                                         /*!< TPI DEVID: PTINVALID Position */
#define TPI_DEVID_PTINVALID_Msk            (0x1UL << TPI_DEVID_PTINVALID_Pos)          /*!< TPI DEVID: PTINVALID Mask */

#define TPI_DEVID_FIFOSZ_Pos                6U                                         /*!< TPI DEVID: FIFO depth Position */
#define TPI_DEVID_FIFOSZ_Msk               (0x7UL << TPI_DEVID_FIFOSZ_Pos)             /*!< TPI DEVID: FIFO depth Mask */

/* TPI DEVTYPE Register Definitions */
#define TPI_DEVTYPE_SubType_Pos             4U                                         /*!< TPI DEVTYPE: SubType Position */
#define TPI_DEVTYPE_SubType_Msk            (0xFUL /*<< TPI_DEVTYPE_SubType_Pos*/)      /*!< TPI DEVTYPE: SubType Mask */

#define TPI_DEVTYPE_MajorType_Pos           0U                                         /*!< TPI DEVTYPE: MajorType Position */
#define TPI_DEVTYPE_MajorType_Msk          (0xFUL << TPI_DEVTYPE_MajorType_Pos)        /*!< TPI DEVTYPE: MajorType Mask */

/*@}*/ /* end of group CMSIS_TPI */


#if defined (__MPU_PRESENT) && (__MPU_PRESENT == 1U)
/**
  \ingroup  CMSIS_core_register
  \defgroup CMSIS_MPU     Memory Protection Unit (MPU)
  \brief    Type definitions for the Memory Protection Unit (MPU)
  @{
 */

/**
  \brief  Structure type to access the Memory Protection Unit (MPU).
 */
typedef struct
{
  __IM  uint32_t TYPE;                   /*!< Offset: 0x000 (R/ )  MPU Type Register */
  __IOM uint32_t CTRL;                   /*!< Offset: 0x004 (R/W)  MPU Control Register */
  __IOM uint32_t RNR;                    /*!< Offset: 0x008 (R/W)  MPU Region Number Register */
  __IOM uint32_t RBAR;                   /*!< Offset: 0x00C (R/W)  MPU Region Base Address Register */
  __IOM uint32_t RLAR;                   /*!< Offset: 0x010 (R/W)  MPU Region Limit Address Register */
  __IOM uint32_t RBAR_A1;                /*!< Offset: 0x014 (R/W)  MPU Region Base Address Register Alias 1 */
  __IOM uint32_t RLAR_A1;                /*!< Offset: 0x018 (R/W)  MPU Region Limit Address Register Alias 1 */
  __IOM uint32_t RBAR_A2;                /*!< Offset: 0x01C (R/W)  MPU Region Base Address Register Alias 2 */
  __IOM uint32_t RLAR_A2;                /*!< Offset: 0x020 (R/W)  MPU Region Limit Address Register Alias 2 */
  __IOM uint32_t RBAR_A3;                /*!< Offset: 0x024 (R/W)  MPU Region Base Address Register Alias 3 */
  __IOM uint32_t RLAR_A3;                /*!< Offset: 0x028 (R/W)  MPU Region Limit Address Register Alias 3 */
        uint32_t RESERVED0[1];
  union {
  __IOM uint32_t MAIR[2];
  struct {
  __IOM uint32_t MAIR0;                  /*!< Offset: 0x030 (R/W)  MPU Memory Attribute Indirection Register 0 */
  __IOM uint32_t MAIR1;                  /*!< Offset: 0x034 (R/W)  MPU Memory Attribute Indirection Register 1 */
  };
  };
} MPU_Type;

#define MPU_TYPE_RALIASES                  4U

/* MPU Type Register Definitions */
#define MPU_TYPE_IREGION_Pos               16U                                            /*!< MPU TYPE: IREGION Position */
#define MPU_TYPE_IREGION_Msk               (0xFFUL << MPU_TYPE_IREGION_Pos)               /*!< MPU TYPE: IREGION Mask */

#define MPU_TYPE_DREGION_Pos                8U                                            /*!< MPU TYPE: DREGION Position */
#define MPU_TYPE_DREGION_Msk               (0xFFUL << MPU_TYPE_DREGION_Pos)               /*!< MPU TYPE: DREGION Mask */

#define MPU_TYPE_SEPARATE_Pos               0U                                            /*!< MPU TYPE: SEPARATE Position */
#define MPU_TYPE_SEPARATE_Msk              (1UL /*<< MPU_TYPE_SEPARATE_Pos*/)             /*!< MPU TYPE: SEPARATE Mask */

/* MPU Control Register Definitions */
#define MPU_CTRL_PRIVDEFENA_Pos             2U                                            /*!< MPU CTRL: PRIVDEFENA Position */
#define MPU_CTRL_PRIVDEFENA_Msk            (1UL << MPU_CTRL_PRIVDEFENA_Pos)               /*!< MPU CTRL: PRIVDEFENA Mask */

#define MPU_CTRL_HFNMIENA_Pos               1U                                            /*!< MPU CTRL: HFNMIENA Position */
#define MPU_CTRL_HFNMIENA_Msk              (1UL << MPU_CTRL_HFNMIENA_Pos)                 /*!< MPU CTRL: HFNMIENA Mask */

#define MPU_CTRL_ENABLE_Pos                 0U                                            /*!< MPU CTRL: ENABLE Position */
#define MPU_CTRL_ENABLE_Msk                (1UL /*<< MPU_CTRL_ENABLE_Pos*/)               /*!< MPU CTRL: ENABLE Mask */

/* MPU Region Number Register Definitions */
#define MPU_RNR_REGION_Pos                  0U                                            /*!< MPU RNR: REGION Position */
#define MPU_RNR_REGION_Msk                 (0xFFUL /*<< MPU_RNR_REGION_Pos*/)             /*!< MPU RNR: REGION Mask */

/* MPU Region Base Address Register Definitions */
#define MPU_RBAR_BASE_Pos                   5U                                            /*!< MPU RBAR: BASE Position */
#define MPU_RBAR_BASE_Msk                  (0x7FFFFFFUL << MPU_RBAR_BASE_Pos)             /*!< MPU RBAR: BASE Mask */

#define MPU_RBAR_SH_Pos                     3U                                            /*!< MPU RBAR: SH Position */
#define MPU_RBAR_SH_Msk                    (0x3UL << MPU_RBAR_SH_Pos)                     /*!< MPU RBAR: SH Mask */

#define MPU_RBAR_AP_Pos                     1U                                            /*!< MPU RBAR: AP Position */
#define MPU_RBAR_AP_Msk                    (0x3UL << MPU_RBAR_AP_Pos)                     /*!< MPU RBAR: AP Mask */

#define MPU_RBAR_XN_Pos                     0U                                            /*!< MPU RBAR: XN Position */
#define MPU_RBAR_XN_Msk                    (01UL /*<< MPU_RBAR_XN_Pos*/)                  /*!< MPU RBAR: XN Mask */

/* MPU Region Limit Address Register Definitions */
#define MPU_RLAR_LIMIT_Pos                  5U                                            /*!< MPU RLAR: LIMIT Position */
#define MPU_RLAR_LIMIT_Msk                 (0x7FFFFFFUL << MPU_RLAR_LIMIT_Pos)            /*!< MPU RLAR: LIMIT Mask */

#define MPU_RLAR_PXN_Pos                    4U                                            /*!< MPU RLAR: PXN Position */
#define MPU_RLAR_PXN_Msk                   (1UL << MPU_RLAR_PXN_Pos)                      /*!< MPU RLAR: PXN Mask */

#define MPU_RLAR_AttrIndx_Pos               1U                                            /*!< MPU RLAR: AttrIndx Position */
#define MPU_RLAR_AttrIndx_Msk              (7UL << MPU_RLAR_AttrIndx_Pos)                 /*!< MPU RLAR: AttrIndx Mask */

#define MPU_RLAR_EN_Pos                     0U                                            /*!< MPU RLAR: Region enable bit Position */
#define MPU_RLAR_EN_Msk                    (1UL /*<< MPU_RLAR_EN_Pos*/)                   /*!< MPU RLAR: Region enable bit Disable Mask */

/* MPU Memory Attribute Indirection Register 0 Definitions */
#define MPU_MAIR0_Attr3_Pos                24U                                            /*!< MPU MAIR0: Attr3 Position */
#define MPU_MAIR0_Attr3_Msk                (0xFFUL << MPU_MAIR0_Attr3_Pos)                /*!< MPU MAIR0: Attr3 Mask */

#define MPU_MAIR0_Attr2_Pos                16U                                            /*!< MPU MAIR0: Attr2 Position */
#define MPU_MAIR0_Attr2_Msk                (0xFFUL << MPU_MAIR0_Attr2_Pos)                /*!< MPU MAIR0: Attr2 Mask */

#define MPU_MAIR0_Attr1_Pos                 8U                                            /*!< MPU MAIR0: Attr1 Position */
#define MPU_MAIR0_Attr1_Msk                (0xFFUL << MPU_MAIR0_Attr1_Pos)                /*!< MPU MAIR0: Attr1 Mask */

#define MPU_MAIR0_Attr0_Pos                 0U                                            /*!< MPU MAIR0: Attr0 Position */
#define MPU_MAIR0_Attr0_Msk                (0xFFUL /*<< MPU_MAIR0_Attr0_Pos*/)            /*!< MPU MAIR0: Attr0 Mask */

/* MPU Memory Attribute Indirection Register 1 Definitions */
#define MPU_MAIR1_Attr7_Pos                24U                                            /*!< MPU MAIR1: Attr7 Position */
#define MPU_MAIR1_Attr7_Msk                (0xFFUL << MPU_MAIR1_Attr7_Pos)                /*!< MPU MAIR1: Attr7 Mask */

#define MPU_MAIR1_Attr6_Pos                16U                                            /*!< MPU MAIR1: Attr6 Position */
#define MPU_MAIR1_Attr6_Msk                (0xFFUL << MPU_MAIR1_Attr6_Pos)                /*!< MPU MAIR1: Attr6 Mask */

#define MPU_MAIR1_Attr5_Pos                 8U                                            /*!< MPU MAIR1: Attr5 Position */
#define MPU_MAIR1_Attr5_Msk                (0xFFUL << MPU_MAIR1_Attr5_Pos)                /*!< MPU MAIR1: Attr5 Mask */

#define MPU_MAIR1_Attr4_Pos                 0U                                            /*!< MPU MAIR1: Attr4 Position */
#define MPU_MAIR1_Attr4_Msk                (0xFFUL /*<< MPU_MAIR1_Attr4_Pos*/)            /*!< MPU MAIR1: Attr4 Mask */

/*@} end of group CMSIS_MPU */
#endif


#if defined (__ARM_FEATURE_CMSE) && (__ARM_FEATURE_CMSE == 3U)
/**
  \ingroup  CMSIS_core_register
  \defgroup CMSIS_SAU     Security Attribution Unit (SAU)
  \brief    Type definitions for the Security Attribution Unit (SAU)
  @{
 */

/**
  \brief  Structure type to access the Security Attribution Unit (SAU).
 */
typedef struct
{
  __IOM uint32_t CTRL;                   /*!< Offset: 0x000 (R/W)  SAU Control Register */
  __IM  uint32_t TYPE;                   /*!< Offset: 0x004 (R/ )  SAU Type Register */
#if defined (__SAUREGION_PRESENT) && (__SAUREGION_PRESENT == 1U)
  __IOM uint32_t RNR;                    /*!< Offset: 0x008 (R/W)  SAU Region Number Register */
  __IOM uint32_t RBAR;                   /*!< Offset: 0x00C (R/W)  SAU Region Base Address Register */
  __IOM uint32_t RLAR;                   /*!< Offset: 0x010 (R/W)  SAU Region Limit Address Register */
#else
        uint32_t RESERVED0[3];
#endif
  __IOM uint32_t SFSR;                   /*!< Offset: 0x014 (R/W)  Secure Fault Status Register */
  __IOM uint32_t SFAR;                   /*!< Offset: 0x018 (R/W)  Secure Fault Address Register */
} SAU_Type;

/* SAU Control Register Definitions */
#define SAU_CTRL_ALLNS_Pos                  1U                                            /*!< SAU CTRL: ALLNS Position */
#define SAU_CTRL_ALLNS_Msk                 (1UL << SAU_CTRL_ALLNS_Pos)                    /*!< SAU CTRL: ALLNS Mask */

#define SAU_CTRL_ENABLE_Pos                 0U                                            /*!< SAU CTRL: ENABLE Position */
#define SAU_CTRL_ENABLE_Msk                (1UL /*<< SAU_CTRL_ENABLE_Pos*/)               /*!< SAU CTRL: ENABLE Mask */

/* SAU Type Register Definitions */
#define SAU_TYPE_SREGION_Pos                0U                                            /*!< SAU TYPE: SREGION Position */
#define SAU_TYPE_SREGION_Msk               (0xFFUL /*<< SAU_TYPE_SREGION_Pos*/)           /*!< SAU TYPE: SREGION Mask */

#if defined (__SAUREGION_PRESENT) && (__SAUREGION_PRESENT == 1U)
/* SAU Region Number Register Definitions */
#define SAU_RNR_REGION_Pos                  0U                                            /*!< SAU RNR: REGION Position */
#define SAU_RNR_REGION_Msk                 (0xFFUL /*<< SAU_RNR_REGION_Pos*/)             /*!< SAU RNR: REGION Mask */

/* SAU Region Base Address Register Definitions */
#define SAU_RBAR_BADDR_Pos                  5U                                            /*!< SAU RBAR: BADDR Position */
#define SAU_RBAR_BADDR_Msk                 (0x7FFFFFFUL << SAU_RBAR_BADDR_Pos)            /*!< SAU RBAR: BADDR Mask */

/* SAU Region Limit Address Register Definitions */
#define SAU_RLAR_LADDR_Pos                  5U                                            /*!< SAU RLAR: LADDR Position */
#define SAU_RLAR_LADDR_Msk                 (0x7FFFFFFUL << SAU_RLAR_LADDR_Pos)            /*!< SAU RLAR: LADDR Mask */

#define SAU_RLAR_NSC_Pos                    1U                                            /*!< SAU RLAR: NSC Position */
#define SAU_RLAR_NSC_Msk                   (1UL << SAU_RLAR_NSC_Pos)                      /*!< SAU RLAR: NSC Mask */

#define SAU_RLAR_ENABLE_Pos                 0U                                            /*!< SAU RLAR: ENABLE Position */
#define SAU_RLAR_ENABLE_Msk                (1UL /*<< SAU_RLAR_ENABLE_Pos*/)               /*!< SAU RLAR: ENABLE Mask */

#endif /* defined (__SAUREGION_PRESENT) && (__SAUREGION_PRESENT == 1U) */

/* Secure Fault Status Register Definitions */
#define SAU_SFSR_LSERR_Pos                  7U                                            /*!< SAU SFSR: LSERR Position */
#define SAU_SFSR_LSERR_Msk                 (1UL << SAU_SFSR_LSERR_Pos)                    /*!< SAU SFSR: LSERR Mask */

#define SAU_SFSR_SFARVALID_Pos              6U                                            /*!< SAU SFSR: SFARVALID Position */
#define SAU_SFSR_SFARVALID_Msk             (1UL << SAU_SFSR_SFARVALID_Pos)                /*!< SAU SFSR: SFARVALID Mask */

#define SAU_SFSR_LSPERR_Pos                 5U                                            /*!< SAU SFSR: LSPERR Position */
#define SAU_SFSR_LSPERR_Msk                (1UL << SAU_SFSR_LSPERR_Pos)                   /*!< SAU SFSR: LSPERR Mask */

#define SAU_SFSR_INVTRAN_Pos                4U                                            /*!< SAU SFSR: INVTRAN Position */
#define SAU_SFSR_INVTRAN_Msk               (1UL << SAU_SFSR_INVTRAN_Pos)                  /*!< SAU SFSR: INVTRAN Mask */

#define SAU_SFSR_AUVIOL_Pos                 3U                                            /*!< SAU SFSR: AUVIOL Position */
#define SAU_SFSR_AUVIOL_Msk                (1UL << SAU_SFSR_AUVIOL_Pos)                   /*!< SAU SFSR: AUVIOL Mask */

#define SAU_SFSR_INVER_Pos                  2U                                            /*!< SAU SFSR: INVER Position */
#define SAU_SFSR_INVER_Msk                 (1UL << SAU_SFSR_INVER_Pos)                    /*!< SAU SFSR: INVER Mask */

#define SAU_SFSR_INVIS_Pos                  1U                                            /*!< SAU SFSR: INVIS Position */
#define SAU_SFSR_INVIS_Msk                 (1UL << SAU_SFSR_INVIS_Pos)                    /*!< SAU SFSR: INVIS Mask */

#define SAU_SFSR_INVEP_Pos                  0U                                            /*!< SAU SFSR: INVEP Position */
#define SAU_SFSR_INVEP_Msk                 (1UL /*<< SAU_SFSR_INVEP_Pos*/)                /*!< SAU SFSR: INVEP Mask */

/*@} end of group CMSIS_SAU */
#endif /* defined (__ARM_FEATURE_CMSE) && (__ARM_FEATURE_CMSE == 3U) */


/**
  \ingroup  CMSIS_core_register
  \defgroup CMSIS_FPU     Floating Point Unit (FPU)
  \brief    Type definitions for the Floating Point Unit (FPU)
  @{
 */

/**
  \brief  Structure type to access the Floating Point Unit (FPU).
 */
typedef struct
{
        uint32_t RESERVED0[1U];
  __IOM uint32_t FPCCR;                  /*!< Offset: 0x004 (R/W)  Floating-Point Context Control Register */
  __IOM uint32_t FPCAR;                  /*!< Offset: 0x008 (R/W)  Floating-Point Context Address Register */
  __IOM uint32_t FPDSCR;                 /*!< Offset: 0x00C (R/W)  Floating-Point Default Status Control Register */
  __IM  uint32_t MVFR0;                  /*!< Offset: 0x010 (R/ )  Media and FP Feature Register 0 */
  __IM  uint32_t MVFR1;                  /*!< Offset: 0x014 (R/ )  Media and FP Feature Register 1 */
  __IM  uint32_t MVFR2;                  /*!< Offset: 0x018 (R/ )  Media and FP Feature Register 2 */
} FPU_Type;

/* Floating-Point Context Control Register Definitions */
#define FPU_FPCCR_ASPEN_Pos                31U                                            /*!< FPCCR: ASPEN bit Position */
#define FPU_FPCCR_ASPEN_Msk                (1UL << FPU_FPCCR_ASPEN_Pos)                   /*!< FPCCR: ASPEN bit Mask */

#define FPU_FPCCR_LSPEN_Pos                30U                                            /*!< FPCCR: LSPEN Position */
#define FPU_FPCCR_LSPEN_Msk                (1UL << FPU_FPCCR_LSPEN_Pos)                   /*!< FPCCR: LSPEN bit Mask */

#define FPU_FPCCR_LSPENS_Pos               29U                                            /*!< FPCCR: LSPENS Position */
#define FPU_FPCCR_LSPENS_Msk               (1UL << FPU_FPCCR_LSPENS_Pos)                  /*!< FPCCR: LSPENS bit Mask */

#define FPU_FPCCR_CLRONRET_Pos             28U                                            /*!< FPCCR: CLRONRET Position */
#define FPU_FPCCR_CLRONRET_Msk             (1UL << FPU_FPCCR_CLRONRET_Pos)                /*!< FPCCR: CLRONRET bit Mask */

#define FPU_FPCCR_CLRONRETS_Pos            27U                                            /*!< FPCCR: CLRONRETS Position */
#define FPU_FPCCR_CLRONRETS_Msk            (1UL << FPU_FPCCR_CLRONRETS_Pos)               /*!< FPCCR: CLRONRETS bit Mask */

#define FPU_FPCCR_TS_Pos                   26U                                            /*!< FPCCR: TS Position */
#define FPU_FPCCR_TS_Msk                   (1UL << FPU_FPCCR_TS_Pos)                      /*!< FPCCR: TS bit Mask */

#define FPU_FPCCR_UFRDY_Pos                10U                                            /*!< FPCCR: UFRDY Position */
#define FPU_FPCCR_UFRDY_Msk                (1UL << FPU_FPCCR_UFRDY_Pos)                   /*!< FPCCR: UFRDY bit Mask */

#define FPU_FPCCR_SPLIMVIOL_Pos             9U                                            /*!< FPCCR: SPLIMVIOL Position */
#define FPU_FPCCR_SPLIMVIOL_Msk            (1UL << FPU_FPCCR_SPLIMVIOL_Pos)               /*!< FPCCR: SPLIMVIOL bit Mask */

#define FPU_FPCCR_MONRDY_Pos                8U                                            /*!< FPCCR: MONRDY Position */
#define FPU_FPCCR_MONRDY_Msk               (1UL << FPU_FPCCR_MONRDY_Pos)                  /*!< FPCCR: MONRDY bit Mask */

#define FPU_FPCCR_SFRDY_Pos                 7U                                            /*!< FPCCR: SFRDY Position */
#define FPU_FPCCR_SFRDY_Msk                (1UL << FPU_FPCCR_SFRDY_Pos)                   /*!< FPCCR: SFRDY bit Mask */

#define FPU_FPCCR_BFRDY_Pos                 6U                                            /*!< FPCCR: BFRDY Position */
#define FPU_FPCCR_BFRDY_Msk                (1UL << FPU_FPCCR_BFRDY_Pos)                   /*!< FPCCR: BFRDY bit Mask */

#define FPU_FPCCR_MMRDY_Pos                 5U                                            /*!< FPCCR: MMRDY Position */
#define FPU_FPCCR_MMRDY_Msk                (1UL << FPU_FPCCR_MMRDY_Pos)                   /*!< FPCCR: MMRDY bit Mask */

#define FPU_FPCCR_HFRDY_Pos                 4U                                            /*!< FPCCR: HFRDY Position */
#define FPU_FPCCR_HFRDY_Msk                (1UL << FPU_FPCCR_HFRDY_Pos)                   /*!< FPCCR: HFRDY bit Mask */

#define FPU_FPCCR_THREAD_Pos                3U                                            /*!< FPCCR: processor mode bit Position */
#define FPU_FPCCR_THREAD_Msk               (1UL << FPU_FPCCR_THREAD_Pos)                  /*!< FPCCR: processor mode active bit Mask */

#define FPU_FPCCR_S_Pos                     2U                                            /*!< FPCCR: Security status of the FP context bit Position */
#define FPU_FPCCR_S_Msk                    (1UL << FPU_FPCCR_S_Pos)                       /*!< FPCCR: Security status of the FP context bit Mask */

#define FPU_FPCCR_USER_Pos                  1U                                            /*!< FPCCR: privilege level bit Position */
#define FPU_FPCCR_USER_Msk                 (1UL << FPU_FPCCR_USER_Pos)                    /*!< FPCCR: privilege level bit Mask */

#define FPU_FPCCR_LSPACT_Pos                0U                                            /*!< FPCCR: Lazy state preservation active bit Position */
#define FPU_FPCCR_LSPACT_Msk               (1UL /*<< FPU_FPCCR_LSPACT_Pos*/)              /*!< FPCCR: Lazy state preservation active bit Mask */

/* Floating-Point Context Address Register Definitions */
#define FPU_FPCAR_ADDRESS_Pos               3U                                            /*!< FPCAR: ADDRESS bit Position */
#define FPU_FPCAR_ADDRESS_Msk              (0x1FFFFFFFUL << FPU_FPCAR_ADDRESS_Pos)        /*!< FPCAR: ADDRESS bit Mask */

/* Floating-Point Default Status Control Register Definitions */
#define FPU_FPDSCR_AHP_Pos                 26U                                            /*!< FPDSCR: AHP bit Position */
#define FPU_FPDSCR_AHP_Msk                 (1UL << FPU_FPDSCR_AHP_Pos)                    /*!< FPDSCR: AHP bit Mask */

#define FPU_FPDSCR_DN_Pos                  25U                                            /*!< FPDSCR: DN bit Position */
#define FPU_FPDSCR_DN_Msk                  (1UL << FPU_FPDSCR_DN_Pos)                     /*!< FPDSCR: DN bit Mask */

#define FPU_FPDSCR_FZ_Pos                  24U                                            /*!< FPDSCR: FZ bit Position */
#define FPU_FPDSCR_FZ_Msk                  (1UL << FPU_FPDSCR_FZ_Pos)                     /*!< FPDSCR: FZ bit Mask */

#define FPU_FPDSCR_RMode_Pos               22U                                            /*!< FPDSCR: RMode bit Position */
#define FPU_FPDSCR_RMode_Msk               (3UL << FPU_FPDSCR_RMode_Pos)                  /*!< FPDSCR: RMode bit Mask */

#define FPU_FPDSCR_FZ16_Pos                19U                                            /*!< FPDSCR: FZ16 bit Position */
#define FPU_FPDSCR_FZ16_Msk                (1UL << FPU_FPDSCR_FZ16_Pos)                   /*!< FPDSCR: FZ16 bit Mask */

#define FPU_FPDSCR_LTPSIZE_Pos             16U                                            /*!< FPDSCR: LTPSIZE bit Position */
#define FPU_FPDSCR_LTPSIZE_Msk             (7UL << FPU_FPDSCR_LTPSIZE_Pos)                /*!< FPDSCR: LTPSIZE bit Mask */

/* Media and FP Feature Register 0 Definitions */
#define FPU_MVFR0_FPRound_Pos              28U                                            /*!< MVFR0: FPRound bits Position */
#define FPU_MVFR0_FPRound_Msk              (0xFUL << FPU_MVFR0_FPRound_Pos)               /*!< MVFR0: FPRound bits Mask */

#define FPU_MVFR0_FPSqrt_Pos               20U                                            /*!< MVFR0: FPSqrt bits Position */
#define FPU_MVFR0_FPSqrt_Msk               (0xFUL << FPU_MVFR0_FPSqrt_Pos)                 /*!< MVFR0: FPSqrt bits Mask */

#define FPU_MVFR0_FPDivide_Pos             16U                                            /*!< MVFR0: FPDivide bits Position */
#define FPU_MVFR0_FPDivide_Msk             (0xFUL << FPU_MVFR0_FPDivide_Pos)              /*!< MVFR0: Divide bits Mask */

#define FPU_MVFR0_FPDP_Pos                  8U                                            /*!< MVFR0: FPDP bits Position */
#define FPU_MVFR0_FPDP_Msk                 (0xFUL << FPU_MVFR0_FPDP_Pos)                  /*!< MVFR0: FPDP bits Mask */

#define FPU_MVFR0_FPSP_Pos                  4U                                            /*!< MVFR0: FPSP bits Position */
#define FPU_MVFR0_FPSP_Msk                 (0xFUL << FPU_MVFR0_FPSP_Pos)                  /*!< MVFR0: FPSP bits Mask */

#define FPU_MVFR0_SIMDReg_Pos               0U                                            /*!< MVFR0: SIMDReg bits Position */
#define FPU_MVFR0_SIMDReg_Msk              (0xFUL /*<< FPU_MVFR0_SIMDReg_Pos*/)           /*!< MVFR0: SIMDReg bits Mask */

/* Media and FP Feature Register 1 Definitions */
#define FPU_MVFR1_FMAC_Pos                 28U                                            /*!< MVFR1: FMAC bits Position */
#define FPU_MVFR1_FMAC_Msk                 (0xFUL << FPU_MVFR1_FMAC_Pos)                  /*!< MVFR1: FMAC bits Mask */

#define FPU_MVFR1_FPHP_Pos                 24U                                            /*!< MVFR1: FPHP bits Position */
#define FPU_MVFR1_FPHP_Msk                 (0xFUL << FPU_MVFR1_FPHP_Pos)                  /*!< MVFR1: FPHP bits Mask */

#define FPU_MVFR1_FP16_Pos                 20U                                            /*!< MVFR1: FP16 bits Position */
#define FPU_MVFR1_FP16_Msk                 (0xFUL << FPU_MVFR1_FP16_Pos)                  /*!< MVFR1: FP16 bits Mask */

#define FPU_MVFR1_MVE_Pos                   8U                                            /*!< MVFR1: MVE bits Position */
#define FPU_MVFR1_MVE_Msk                  (0xFUL << FPU_MVFR1_MVE_Pos)                   /*!< MVFR1: MVE bits Mask */

#define FPU_MVFR1_FPDNaN_Pos                4U                                            /*!< MVFR1: FPDNaN bits Position */
#define FPU_MVFR1_FPDNaN_Msk               (0xFUL << FPU_MVFR1_FPDNaN_Pos)                /*!< MVFR1: FPDNaN bits Mask */

#define FPU_MVFR1_FPFtZ_Pos                 0U                                            /*!< MVFR1: FPFtZ bits Position */
#define FPU_MVFR1_FPFtZ_Msk                (0xFUL /*<< FPU_MVFR1_FPFtZ_Pos*/)             /*!< MVFR1: FPFtZ bits Mask */

/* Media and FP Feature Register 2 Definitions */
#define FPU_MVFR2_FPMisc_Pos                4U                                            /*!< MVFR2: FPMisc bits Position */
#define FPU_MVFR2_FPMisc_Msk               (0xFUL << FPU_MVFR2_FPMisc_Pos)                /*!< MVFR2: FPMisc bits Mask */

/*@} end of group CMSIS_FPU */


/**
  \ingroup  CMSIS_core_register
  \defgroup CMSIS_CoreDebug       Core Debug Registers (CoreDebug)
  \brief    Type definitions for the Core Debug Registers
  @{
 */

/**
  \brief  Structure type to access the Core Debug Register (CoreDebug).
 */
typedef struct
{
  __IOM uint32_t DHCSR;                  /*!< Offset: 0x000 (R/W)  Debug Halting Control and Status Register */
  __OM  uint32_t DCRSR;                  /*!< Offset: 0x004 ( /W)  Debug Core Register Selector Register */
  __IOM uint32_t DCRDR;                  /*!< Offset: 0x008 (R/W)  Debug Core Register Data Register */
  __IOM uint32_t DEMCR;                  /*!< Offset: 0x00C (R/W)  Debug Exception and Monitor Control Register */
  __OM  uint32_t DSCEMCR;                /*!< Offset: 0x010 ( /W)  Debug Set Clear Exception and Monitor Control Register */
  __IOM uint32_t DAUTHCTRL;              /*!< Offset: 0x014 (R/W)  Debug Authentication Control Register */
  __IOM uint32_t DSCSR;                  /*!< Offset: 0x018 (R/W)  Debug Security Control and Status Register */
} CoreDebug_Type;

/* Debug Halting Control and Status Register Definitions */
#define CoreDebug_DHCSR_DBGKEY_Pos         16U                                            /*!< CoreDebug DHCSR: DBGKEY Position */
#define CoreDebug_DHCSR_DBGKEY_Msk         (0xFFFFUL << CoreDebug_DHCSR_DBGKEY_Pos)       /*!< CoreDebug DHCSR: DBGKEY Mask */

#define CoreDebug_DHCSR_S_RESTART_ST_Pos   26U                                            /*!< CoreDebug DHCSR: S_RESTART_ST Position */
#define CoreDebug_DHCSR_S_RESTART_ST_Msk   (1UL << CoreDebug_DHCSR_S_RESTART_ST_Pos)      /*!< CoreDebug DHCSR: S_RESTART_ST Mask */

#define CoreDebug_DHCSR_S_RESET_ST_Pos     25U                                            /*!< CoreDebug DHCSR: S_RESET_ST Position */
#define CoreDebug_DHCSR_S_RESET_ST_Msk     (1UL << CoreDebug_DHCSR_S_RESET_ST_Pos)        /*!< CoreDebug DHCSR: S_RESET_ST Mask */

#define CoreDebug_DHCSR_S_RETIRE_ST_Pos    24U                                            /*!< CoreDebug DHCSR: S_RETIRE_ST Position */
#define CoreDebug_DHCSR_S_RETIRE_ST_Msk    (1UL << CoreDebug_DHCSR_S_RETIRE_ST_Pos)       /*!< CoreDebug DHCSR: S_RETIRE_ST Mask */

#define CoreDebug_DHCSR_S_FPD_Pos          23U                                            /*!< CoreDebug DHCSR: S_FPD Position */
#define CoreDebug_DHCSR_S_FPD_Msk          (1UL << CoreDebug_DHCSR_S_FPD_Pos)           /*!< CoreDebug DHCSR: S_FPD Mask */

#define CoreDebug_DHCSR_S_SUIDE_Pos        22U                                            /*!< CoreDebug DHCSR: S_SUIDE Position */
#define CoreDebug_DHCSR_S_SUIDE_Msk        (1UL << CoreDebug_DHCSR_S_SUIDE_Pos)           /*!< CoreDebug DHCSR: S_SUIDE Mask */

#define CoreDebug_DHCSR_S_NSUIDE_Pos       21U                                            /*!< CoreDebug DHCSR: S_NSUIDE Position */
#define CoreDebug_DHCSR_S_NSUIDE_Msk       (1UL << CoreDebug_DHCSR_S_NSUIDE_Pos)          /*!< CoreDebug DHCSR: S_NSUIDE Mask */

#define CoreDebug_DHCSR_S_SDE_Pos          20U                                            /*!< CoreDebug DHCSR: S_SDE Position */
#define CoreDebug_DHCSR_S_SDE_Msk          (1UL << CoreDebug_DHCSR_S_SDE_Pos)             /*!< CoreDebug DHCSR: S_SDE Mask */

#define CoreDebug_DHCSR_S_LOCKUP_Pos       19U                                            /*!< CoreDebug DHCSR: S_LOCKUP Position */
#define CoreDebug_DHCSR_S_LOCKUP_Msk       (1UL << CoreDebug_DHCSR_S_LOCKUP_Pos)          /*!< CoreDebug DHCSR: S_LOCKUP Mask */

#define CoreDebug_DHCSR_S_SLEEP_Pos        18U                                            /*!< CoreDebug DHCSR: S_SLEEP Position */
#define CoreDebug_DHCSR_S_SLEEP_Msk        (1UL << CoreDebug_DHCSR_S_SLEEP_Pos)           /*!< CoreDebug DHCSR: S_SLEEP Mask */

#define CoreDebug_DHCSR_S_HALT_Pos         17U                                            /*!< CoreDebug DHCSR: S_HALT Position */
#define CoreDebug_DHCSR_S_HALT_Msk         (1UL << CoreDebug_DHCSR_S_HALT_Pos)            /*!< CoreDebug DHCSR: S_HALT Mask */

#define CoreDebug_DHCSR_S_REGRDY_Pos       16U                                            /*!< CoreDebug DHCSR: S_REGRDY Position */
#define CoreDebug_DHCSR_S_REGRDY_Msk       (1UL << CoreDebug_DHCSR_S_REGRDY_Pos)          /*!< CoreDebug DHCSR: S_REGRDY Mask */

#define CoreDebug_DHCSR_C_PMOV_Pos          6U                                            /*!< CoreDebug DHCSR: C_PMOV Position */
#define CoreDebug_DHCSR_C_PMOV_Msk         (1UL << CoreDebug_DHCSR_C_PMOV_Pos)            /*!< CoreDebug DHCSR: C_PMOV Mask */

#define CoreDebug_DHCSR_C_SNAPSTALL_Pos     5U                                            /*!< CoreDebug DHCSR: C_SNAPSTALL Position */
#define CoreDebug_DHCSR_C_SNAPSTALL_Msk    (1UL << CoreDebug_DHCSR_C_SNAPSTALL_Pos)       /*!< CoreDebug DHCSR: C_SNAPSTALL Mask */
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
