peng-zhihui/L-ink_Card/Firmware/Keil/L-ink_Card/Inc/main.h

#define LED_Pin GPIO_PIN_2
#define LED_GPIO_Port GPIOA
#define ST25_GPO_Pin GPIO_PIN_3
#define ST25_GPO_GPIO_Port GPIOA
#define ST25_GPO_EXTI_IRQn EXTI2_3_IRQn
#define ST25_LPD_Pin GPIO_PIN_4
#define ST25_LPD_GPIO_Port GPIOA
#define INK_MOSI_Pin GPIO_PIN_5
#define INK_MOSI_GPIO_Port GPIOA
#define INK_CLK_Pin GPIO_PIN_6
#define INK_CLK_GPIO_Port GPIOA
#define INK_CS_Pin GPIO_PIN_7
#define INK_CS_GPIO_Port GPIOA
#define INK_DC_Pin GPIO_PIN_0
#define INK_DC_GPIO_Port GPIOB
#define INK_RST_Pin GPIO_PIN_1
#define INK_RST_GPIO_Port GPIOB
#define INK_IS_BUSY_Pin GPIO_PIN_8
#define INK_IS_BUSY_GPIO_Port GPIOA
