peng-zhihui/L-ink_Card/DAP-Link/Firmware/src/source/daplink/drag-n-drop/flash_manager.c

/**
 * @file    flash_manager.c
 * @brief   Implementation of flash_manager.h
 *
 * DAPLink Interface Firmware
 * Copyright (c) 2009-2019, ARM Limited, All Rights Reserved
 * Copyright 2019, Cypress Semiconductor Corporation 
 * or a subsidiary of Cypress Semiconductor Corporation.
 * SPDX-License-Identifier: Apache-2.0
 *
 * Licensed under the Apache License, Version 2.0 (the "License"); you may
 * not use this file except in compliance with the License.
 * You may obtain a copy of the License at
 *
 * http://www.apache.org/licenses/LICENSE-2.0
 *
 * Unless required by applicable law or agreed to in writing, software
 * distributed under the License is distributed on an "AS IS" BASIS, WITHOUT
 * WARRANTIES OR CONDITIONS OF ANY KIND, either express or implied.
 * See the License for the specific language governing permissions and
 * limitations under the License.
 */

#include "flash_manager.h"
#include "util.h"
#include "error.h"
#include "settings.h"

// Set to 1 to enable debugging
#define DEBUG_FLASH_MANAGER     0

#if DEBUG_FLASH_MANAGER
#include "daplink_debug.h"
#define flash_manager_printf    debug_msg
#else
#define flash_manager_printf(...)
#endif

typedef enum {
    STATE_CLOSED,
    STATE_OPEN,
    STATE_ERROR
} state_t;

// Target programming expects buffer
// passed in to be 4 byte aligned
__attribute__((aligned(4)))
static uint8_t buf[1024];
static bool buf_empty;
static bool current_sector_valid;
static bool page_erase_enabled = false;
static uint32_t current_write_block_addr;
static uint32_t current_write_block_size;
static uint32_t current_sector_addr;
static uint32_t current_sector_size;
static uint32_t last_addr;
static const flash_intf_t *intf;
static state_t state = STATE_CLOSED;

static bool flash_intf_valid(const flash_intf_t *flash_intf);
static error_t flush_current_block(uint32_t addr);
static error_t setup_next_sector(uint32_t addr);
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
